CaptainOrangeSparrow/early-fire-detection-classifier/data-recording/test_recordings/recording_test1_25fps_2026-01-25_001_1769378462_16-01-02/adc.csv

frame_idx | t_sample_perf_counter | t_reg_frame | t_ir_frame | t_adc_sweep | adc_sweep_dt_s | adc0_ch0 | adc0_ch1 | adc0_ch2 | adc0_ch3 | adc1_ch0 | adc1_ch1 | adc1_ch2 | adc1_ch3
0 | 330822.027834353 | 330821.990827732 | 330821.979749989 | 330822.005690260 | 0.033709 | 1766 | 276 | 525 | 4731 | 4698 | 4576 | 4306 | 4996
1 | 330822.054127146 | 330822.030868044 | 330822.028520774 | 330822.005690260 | 0.033709 | 1766 | 276 | 525 | 4731 | 4698 | 4576 | 4306 | 4996
2 | 330822.098113978 | 330822.070159758 | 330822.059541134 | 330822.054615641 | 0.048897 | 1768 | 278 | 415 | 4648 | 4649 | 5047 | 4873 | 4268
3 | 330822.135324798 | 330822.110263209 | 330822.103432507 | 330822.091736442 | 0.037081 | 1766 | 278 | 469 | 4710 | 4795 | 4627 | 4168 | 5340
4 | 330822.172963694 | 330822.151891794 | 330822.140606781 | 330822.141824866 | 0.050006 | 1768 | 276 | 37 | 4605 | 4780 | 5144 | 4369 | 5233
5 | 330822.211742912 | 330822.191142963 | 330822.180607316 | 330822.181264712 | 0.039399 | 1767 | 279 | 423 | 4747 | 4698 | 4198 | 5421 | 4541
6 | 330822.252840793 | 330822.230302481 | 330822.220466344 | 330822.224948879 | 0.043629 | 1767 | 278 | 275 | 4694 | 4779 | 4375 | 4636 | 5089
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
