CaptainOrangeSparrow/early-fire-detection-classifier/data-recording/test_recordings/recording_test2_25fps_2026-01-26_001_1769410458_00-54-18/adc.csv

frame_idx | t_sample_perf_counter | t_reg_frame | t_ir_frame | t_adc_sweep | adc_sweep_dt_s | adc0_ch0 | adc0_ch1 | adc0_ch2 | adc0_ch3 | adc1_ch0 | adc1_ch1 | adc1_ch2 | adc1_ch3 | ir_min | ir_max | ir_avg | ir_center
0 | 362818.315297676 | 362818.274354627 | 362818.274255493 | 362818.278961247 | 0.032010 | 1736 | 286 | 373 | 4764 | 4706 | 4060 | 4685 | 5079 | 29.54 | 34.85 | 29.16 | 31.79 | INFERNO
1 | 362818.346244781 | 362818.336293317 | 362818.321560484 | 362818.325076888 | 0.046095 | 1732 | 284 | 395 | 4753 | 4766 | 4381 | 4127 | 4689 | 29.54 | 34.85 | 29.16 | 31.79 | INFERNO
2 | 362818.375747725 | 362818.336293317 | 362818.355587618 | 362818.362441390 | 0.037324 | 1734 | 285 | 326 | 4765 | 4712 | 4212 | 4680 | 5129 | 29.54 | 34.85 | 29.16 | 31.79 | INFERNO
3 | 362818.411751777 | 362818.403582482 | 362818.392606656 | 362818.405002803 | 0.042525 | 1734 | 286 | 156 | 4703 | 4614 | 5159 | 4792 | 4072 | 29.54 | 34.91 | 29.16 | 31.79 | INFERNO
4 | 362818.451165835 | 362818.435829655 | 362818.433273070 | 362818.405002803 | 0.042525 | 1734 | 286 | 156 | 4703 | 4614 | 5159 | 4792 | 4072 | 29.54 | 34.91 | 29.16 | 31.85 | INFERNO
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
