CaptainOrangeSparrow/early-fire-detection-classifier/data-recording/test_recordings/recording_test3_25fps_2026-01-26_004_1769415911_02-25-11/adc.csv

frame_idx | t_sample_perf_counter | t_reg_frame | t_ir_frame | t_adc_sweep | adc_sweep_dt_s | adc0_ch0 | adc0_ch1 | adc0_ch2 | adc0_ch3 | adc1_ch0 | adc1_ch1 | adc1_ch2 | adc1_ch3 | ir_min | ir_max | ir_avg | ir_center
0 | 368270.703455939 | 368270.672152276 | 368270.657761993 | 368270.662456597 | 0.029226 | 1750 | 286 | 345 | 4730 | 4745 | 4840 | 4552 | 4217 | 28.662500000000023 | 38.85000000000002 | 31.905227915446005 | 30.787500000000023
1 | 368270.741902709 | 368270.707983723 | 368270.695729905 | 368270.706421223 | 0.043924 | 1748 | 285 | 152 | 4675 | 4736 | 5021 | 4195 | 4840 | 28.662500000000023 | 38.85000000000002 | 31.90362701416018 | 30.787500000000023
2 | 368270.781056152 | 368270.741982071 | 368270.736752607 | 368270.746458814 | 0.039984 | 1749 | 285 | 189 | 4731 | 4667 | 5036 | 4758 | 4454 | 28.662500000000023 | 38.85000000000002 | 31.905603027343773 | 30.787500000000023
3 | 368270.808612145 | 368270.778411964 | 368270.778609728 | 368270.784546505 | 0.038049 | 1747 | 286 | 158 | 4716 | 4793 | 4839 | 4097 | 5117 | 28.662500000000023 | 38.85000000000002 | 31.90813471476241 | 30.787500000000023
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
