CaptainOrangeSparrow/early-fire-detection-classifier/data-recording/test_recordings/recording_test4_25fps_2026-01-26_006_1769417922_02-58-42/adc.csv

frame_idx | t_sample_perf_counter | t_reg_frame | t_ir_frame | t_adc_sweep | adc_sweep_dt_s | adc0_ch0 | adc0_ch1 | adc0_ch2 | adc0_ch3 | adc1_ch0 | adc1_ch1 | adc1_ch2 | adc1_ch3 | ir_min | ir_max | ir_avg | ir_center
0 | 370282.103740128 | 370282.087772986 | 370282.070901916 | 370282.071093409 | 0.032481 | 1765 | 286 | 156 | 4676 | 4597 | 4967 | 5038 | 4580 | 28.787500000000023 | 39.66250000000002 | 32.59181493123373 | 35.60000000000002
1 | 370282.134913529 | 370282.119331005 | 370282.121138348 | 370282.122146151 | 0.051032 | 1764 | 287 | 149 | 4679 | 4758 | 4979 | 5207 | 4467 | 28.787500000000023 | 39.60000000000002 | 32.59319966634115 | 35.66250000000002
2 | 370282.174606962 | 370282.153983537 | 370282.151795159 | 370282.162097576 | 0.039929 | 1763 | 287 | 151 | 4648 | 4815 | 4804 | 4159 | 4946 | 28.662500000000023 | 39.60000000000002 | 32.59789174397787 | 35.66250000000002
3 | 370282.215379016 | 370282.189044624 | 370282.193560103 | 370282.201662334 | 0.039540 | 1762 | 287 | 372 | 4745 | 4722 | 4273 | 4955 | 4913 | 28.787500000000023 | 39.60000000000002 | 32.59856948852541 | 35.66250000000002
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
