CaptainOrangeSparrow/early-fire-detection-classifier/data-recording/test_recordings/recording_test4_25fps_2026-01-26_008_1769418220_03-03-40/adc.csv

frame_idx | t_sample_perf_counter | t_reg_frame | t_ir_frame | t_adc_sweep | adc_sweep_dt_s | adc0_ch0 | adc0_ch1 | adc0_ch2 | adc0_ch3 | adc1_ch0 | adc1_ch1 | adc1_ch2 | adc1_ch3 | ir_min | ir_max | ir_avg | ir_center
0 | 370579.990639733 | 370579.981060264 | 370579.969358592 | 370579.971925576 | 0.034163 | 1762 | 286 | 342 | 4736 | 4790 | 4689 | 4121 | 4773 | 28.412500000000023 | 39.97500000000002 | 33.46427815755209 | 34.16250000000002
1 | 370580.021041448 | 370579.981060264 | 370580.003070193 | 370580.010112342 | 0.038144 | 1760 | 286 | 394 | 4757 | 4697 | 4074 | 4895 | 5138 | 28.412500000000023 | 39.91250000000002 | 33.46760203043624 | 34.10000000000002
2 | 370580.057584488 | 370580.048676398 | 370580.042907949 | 370580.047195525 | 0.037045 | 1758 | 289 | 188 | 4705 | 4571 | 4800 | 5155 | 4717 | 28.412500000000023 | 39.91250000000002 | 33.469607289632165 | 34.16250000000002
3 | 370580.098984943 | 370580.081017304 | 370580.083453660 | 370580.084930150 | 0.037696 | 1761 | 287 | 153 | 4648 | 4710 | 5078 | 4811 | 3926 | 28.412500000000023 | 39.97500000000002 | 33.46836751302084 | 34.16250000000002
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
