CaptainOrangeSparrow/early-fire-detection-classifier/data-recording/test_recordings/recording_test4_25fps_2026-01-26_009_1769418456_03-07-36/adc.csv

frame_idx | t_sample_perf_counter | t_reg_frame | t_ir_frame | t_adc_sweep | adc_sweep_dt_s | adc0_ch0 | adc0_ch1 | adc0_ch2 | adc0_ch3 | adc1_ch0 | adc1_ch1 | adc1_ch2 | adc1_ch3 | ir_min | ir_max | ir_avg | ir_center
0 | 370816.171426577 | 370816.158830439 | 370816.151630872 | 370816.151178059 | 0.031555 | 1765 | 287 | 160 | 4658 | 4723 | 5076 | 4610 | 4182 | 28.412500000000023 | 40.10000000000002 | 33.568388875325525 | 34.28750000000002
1 | 370816.208314229 | 370816.190736412 | 370816.185745325 | 370816.183391017 | 0.032158 | 1760 | 288 | 169 | 4640 | 4713 | 5067 | 4775 | 4292 | 28.412500000000023 | 40.10000000000002 | 33.57233327229818 | 34.28750000000002
2 | 370816.251142725 | 370816.222527054 | 370816.222872152 | 370816.223453417 | 0.039980 | 1763 | 288 | 155 | 4630 | 4791 | 4768 | 4183 | 4876 | 28.475000000000023 | 40.03750000000002 | 33.575635528564476 | 34.28750000000002
3 | 370816.285731015 | 370816.259526070 | 370816.264908496 | 370816.265819467 | 0.042327 | 1762 | 288 | 410 | 4767 | 4615 | 4898 | 5128 | 4460 | 28.412500000000023 | 40.03750000000002 | 33.57968165079757 | 34.28750000000002
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
