CaptainOrangeSparrow/early-fire-detection-classifier/data-recording/test_recordings/recording_test_25fps_2026-01-21_001_1769058135_23-02-15/adc.csv

frame_idx | t_sample_perf_counter | t_reg_frame | t_ir_frame | t_adc_sweep | adc_sweep_dt_s | adc0_ch0 | adc0_ch1 | adc0_ch2 | adc0_ch3 | adc1_ch0 | adc1_ch1 | adc1_ch2 | adc1_ch3
0 | 10494.949746390 | 10494.907329382 | 10494.903052842 | 10494.933231130 | 0.003040 | 1950 | 1950 | 1950 | 1951 | 4840 | 4840 | 4840 | 4788
1 | 10495.004708112 | 10494.991006075 | 10494.985168613 | 10494.991586640 | 0.007549 | -97 | -97 | 1953 | 1953 | 4575 | 4575 | 4575 | 3997
2 | 10495.057073772 | 10495.026786808 | 10495.025353987 | 10495.046790867 | 0.005011 | 1950 | 1950 | 1950 | 1951 | 4275 | 4819 | 4819 | 5286
3 | 10495.107634916 | 10495.067208830 | 10495.066076565 | 10495.094851888 | 0.003638 | 4573 | 4573 | 4573 | 1949 | 4506 | 4506 | 4506 | 4752
4 | 10495.186658412 | 10495.146546674 | 10495.143366686 | 10495.171375485 | 0.003505 | 1951 | 1951 | 1951 | 1950 | 4756 | 4756 | 4756 | 4611
5 | 10495.391040474 | 10495.348359074 | 10495.349316869 | 10495.377984029 | 0.003810 | 4557 | 4557 | 4557 | 1952 | 4020 | 4020 | 4785 | 4785
6 | 10495.638636916 | 10495.626928072 | 10495.625272300 | 10495.625371119 | 0.004291 | 4738 | 4738 | 1947 | 1947 | 4782 | 4782 | 4782 | 4505
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
