CaptainOrangeSparrow/early-fire-detection-classifier/data-recording/test_recordings/recording_test_25fps_2026-01-21_001_1769059369_23-22-49/adc.csv

frame_idx | t_sample_perf_counter | t_reg_frame | t_ir_frame | t_adc_sweep | adc_sweep_dt_s | adc0_ch0 | adc0_ch1 | adc0_ch2 | adc0_ch3 | adc1_ch0 | adc1_ch1 | adc1_ch2 | adc1_ch3
0 | 11728.372083297 | 11728.309998510 | 11728.316491082 | 11728.347690072 | 0.003868 | 1969 | 1969 | 1969 | 1969 | 4903 | 4903 | 4496 | 4496
1 | 11728.438461084 | 11728.397349920 | 11728.396888789 | 11728.415118283 | 0.004349 | 4651 | 4651 | 4651 | 1968 | 4004 | 4004 | 4004 | 4583
2 | 11728.859521468 | 11728.830881868 | 11728.833372904 | 11728.840672504 | 0.004829 | 4720 | 4720 | 1965 | 1965 | 5389 | 4825 | 4825 | 4825
3 | 11728.918410275 | 11728.872345392 | 11728.874372673 | 11728.896403218 | 0.003807 | 4697 | 4697 | 4697 | 1966 | 4485 | 4485 | 4485 | 4547
4 | 11728.975548575 | 11728.949906871 | 11728.958007962 | 11728.963948360 | 0.004277 | 4615 | 4615 | 4615 | 1970 | 4494 | 4494 | 4494 | 4486
5 | 11729.096966659 | 11729.070986387 | 11729.073584753 | 11729.086172992 | 0.004196 | 1971 | 1971 | 1971 | 1966 | 4675 | 4675 | 4797 | 4797
6 | 11729.372172756 | 11729.351712041 | 11729.353456306 | 11729.360128403 | 0.006108 | 4733 | 4733 | 1968 | 1968 | 5506 | 5506 | 5506 | 4686
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
