CaptainOrangeSparrow/early-fire-detection-classifier/data-recording/test_recordings/recording_test_25fps_2026-01-21_001_1769059793_23-29-53/adc.csv

frame_idx | t_sample_perf_counter | t_reg_frame | t_ir_frame | t_adc_sweep | adc_sweep_dt_s | adc0_ch0 | adc0_ch1 | adc0_ch2 | adc0_ch3 | adc1_ch0 | adc1_ch1 | adc1_ch2 | adc1_ch3
0 | 12152.533478815 | 12152.484226626 | 12152.516361647 | 12152.519658268 | 0.007183 | 1997 | 1997 | 1997 | 1997 | 4787 | 4787 | 4787 | 4528
1 | 12152.582394835 | 12152.565887090 | 12152.555753638 | 12152.571952544 | 0.006308 | 20688 | 20688 | 1995 | 1995 | 4458 | 4502 | 4502 | 4163
2 | 12152.678206958 | 12152.643040954 | 12152.637206642 | 12152.655680384 | 0.005038 | 3 | 3 | 3 | 4536 | 4223 | 4223 | 4548 | 4548
3 | 12152.765593732 | 12152.723165638 | 12152.717661510 | 12152.744185648 | 0.004588 | 1997 | 1997 | 1997 | 1995 | 4549 | 4912 | 4912 | 4912
4 | 12152.854543102 | 12152.805680171 | 12152.837284812 | 12152.839445246 | 0.006926 | 1995 | 1995 | 1995 | 1995 | 5150 | 5150 | 4483 | 4483
5 | 12153.002703741 | 12152.963346887 | 12152.955612051 | 12152.992445134 | 0.005571 | 4647 | 4647 | 4647 | 1993 | 4044 | 4044 | 4714 | 4714
6 | 12153.222225276 | 12153.203129855 | 12153.197926566 | 12153.208913350 | 0.005056 | 1996 | 1996 | 1996 | 1994 | 4143 | 4143 | 4854 | 4854
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
