CaptainOrangeSparrow/early-fire-detection-classifier/data-recording/test_recordings/recording_test_25fps_2026-01-21_001_1769060731_23-45-31/adc.csv

frame_idx | t_sample_perf_counter | t_reg_frame | t_ir_frame | t_adc_sweep | adc_sweep_dt_s | adc0_ch0 | adc0_ch1 | adc0_ch2 | adc0_ch3 | adc1_ch0 | adc1_ch1 | adc1_ch2 | adc1_ch3
0 | 13090.108250302 | 13090.078779330 | 13090.080440176 | 0.000000000 | 0.000000 | -1 | -1 | -1 | -1 | -1 | -1 | -1 | -1
1 | 13090.179703396 | 13090.116375029 | 13090.113490846 | 0.000000000 | 0.000000 | -1 | -1 | -1 | -1 | -1 | -1 | -1 | -1
2 | 13090.228121334 | 13090.197562077 | 13090.193768408 | 0.000000000 | 0.000000 | -1 | -1 | -1 | -1 | -1 | -1 | -1 | -1
3 | 13090.267418650 | 13090.237701866 | 13090.235034053 | 0.000000000 | 0.000000 | -1 | -1 | -1 | -1 | -1 | -1 | -1 | -1
4 | 13090.351544510 | 13090.319131366 | 13090.314027697 | 0.000000000 | 0.000000 | -1 | -1 | -1 | -1 | -1 | -1 | -1 | -1
5 | 13090.558943324 | 13090.519828295 | 13090.521465971 | 0.000000000 | 0.000000 | -1 | -1 | -1 | -1 | -1 | -1 | -1 | -1
6 | 13090.742991723 | 13090.718182367 | 13090.717482531 | 0.000000000 | 0.000000 | -1 | -1 | -1 | -1 | -1 | -1 | -1 | -1
7 | 13090.966249208 | 13090.918611593 | 13090.917398401 | 0.000000000 | 0.000000 | -1 | -1 | -1 | -1 | -1 | -1 | -1 | -1
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
