CaptainOrangeSparrow/early-fire-detection-classifier/data-recording/test_recordings/recording_test_25fps_2026-01-21_001_1769060785_23-46-25/adc.csv

frame_idx | t_sample_perf_counter | t_reg_frame | t_ir_frame | t_adc_sweep | adc_sweep_dt_s | adc0_ch0 | adc0_ch1 | adc0_ch2 | adc0_ch3 | adc1_ch0 | adc1_ch1 | adc1_ch2 | adc1_ch3
0 | 13144.571778375 | 13144.519812500 | 13144.554917660 | 0.000000000 | 0.000000 | -1 | -1 | -1 | -1 | -1 | -1 | -1 | -1
1 | 13144.632439717 | 13144.599915378 | 13144.591252905 | 0.000000000 | 0.000000 | -1 | -1 | -1 | -1 | -1 | -1 | -1 | -1
2 | 13144.960925557 | 13144.918225436 | 13144.913518809 | 0.000000000 | 0.000000 | -1 | -1 | -1 | -1 | -1 | -1 | -1 | -1
3 | 13145.023548501 | 13144.999323116 | 13144.996250575 | 0.000000000 | 0.000000 | -1 | -1 | -1 | -1 | -1 | -1 | -1 | -1
4 | 13145.075746650 | 13145.039747753 | 13145.041411922 | 0.000000000 | 0.000000 | -1 | -1 | -1 | -1 | -1 | -1 | -1 | -1
5 | 13145.159210951 | 13145.117830942 | 13145.115249737 | 0.000000000 | 0.000000 | -1 | -1 | -1 | -1 | -1 | -1 | -1 | -1
6 | 13145.278762955 | 13145.238295565 | 13145.233728405 | 0.000000000 | 0.000000 | -1 | -1 | -1 | -1 | -1 | -1 | -1 | -1
7 | 13145.465502243 | 13145.438903096 | 13145.433419926 | 0.000000000 | 0.000000 | -1 | -1 | -1 | -1 | -1 | -1 | -1 | -1
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
