CaptainOrangeSparrow/early-fire-detection-classifier/data-recording/test_recordings/recording_test_25fps_2026-01-21_001_1769060844_23-47-24/adc.csv

frame_idx | t_sample_perf_counter | t_reg_frame | t_ir_frame | t_adc_sweep | adc_sweep_dt_s | adc0_ch0 | adc0_ch1 | adc0_ch2 | adc0_ch3 | adc1_ch0 | adc1_ch1 | adc1_ch2 | adc1_ch3
0 | 13203.809093113 | 13203.793217171 | 13203.794734347 | 0.000000000 | 0.000000 | -1 | -1 | -1 | -1 | -1 | -1 | -1 | -1
1 | 13203.868863978 | 13203.829321879 | 13203.830461105 | 0.000000000 | 0.000000 | -1 | -1 | -1 | -1 | -1 | -1 | -1 | -1
2 | 13203.951978382 | 13203.910744085 | 13203.913265117 | 0.000000000 | 0.000000 | -1 | -1 | -1 | -1 | -1 | -1 | -1 | -1
3 | 13204.023067293 | 13203.990860973 | 13203.996427813 | 0.000000000 | 0.000000 | -1 | -1 | -1 | -1 | -1 | -1 | -1 | -1
4 | 13204.067859374 | 13204.030996111 | 13204.034820733 | 0.000000000 | 0.000000 | -1 | -1 | -1 | -1 | -1 | -1 | -1 | -1
5 | 13204.262495089 | 13204.231787385 | 13204.235281325 | 0.000000000 | 0.000000 | -1 | -1 | -1 | -1 | -1 | -1 | -1 | -1
6 | 13204.413368789 | 13204.390175790 | 13204.397890511 | 0.000000000 | 0.000000 | -1 | -1 | -1 | -1 | -1 | -1 | -1 | -1
7 | 13204.650052942 | 13204.630918984 | 13204.633744967 | 0.000000000 | 0.000000 | -1 | -1 | -1 | -1 | -1 | -1 | -1 | -1
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
