CaptainOrangeSparrow/early-fire-detection-classifier/data-recording/test_recordings/recording_test_25fps_2026-01-21_001_1769060875_23-47-55/adc.csv

frame_idx | t_sample_perf_counter | t_reg_frame | t_ir_frame | t_adc_sweep | adc_sweep_dt_s | adc0_ch0 | adc0_ch1 | adc0_ch2 | adc0_ch3 | adc1_ch0 | adc1_ch1 | adc1_ch2 | adc1_ch3
0 | 13234.169925595 | 13234.134877443 | 13234.151959149 | 0.000000000 | 0.000000 | -1 | -1 | -1 | -1 | -1 | -1 | -1 | -1
1 | 13234.244147372 | 13234.215262897 | 13234.192547762 | 0.000000000 | 0.000000 | -1 | -1 | -1 | -1 | -1 | -1 | -1 | -1
2 | 13234.291877915 | 13234.252970231 | 13234.271006283 | 0.000000000 | 0.000000 | -1 | -1 | -1 | -1 | -1 | -1 | -1 | -1
3 | 13234.339056766 | 13234.293351725 | 13234.311940331 | 0.000000000 | 0.000000 | -1 | -1 | -1 | -1 | -1 | -1 | -1 | -1
4 | 13234.416914313 | 13234.373577742 | 13234.391272520 | 0.000000000 | 0.000000 | -1 | -1 | -1 | -1 | -1 | -1 | -1 | -1
5 | 13234.617234714 | 13234.573635595 | 13234.591956053 | 0.000000000 | 0.000000 | -1 | -1 | -1 | -1 | -1 | -1 | -1 | -1
6 | 13234.805730744 | 13234.774198671 | 13234.752842426 | 0.000000000 | 0.000000 | -1 | -1 | -1 | -1 | -1 | -1 | -1 | -1
7 | 13235.024958528 | 13234.973918450 | 13234.998075199 | 0.000000000 | 0.000000 | -1 | -1 | -1 | -1 | -1 | -1 | -1 | -1
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
