CaptainOrangeSparrow/early-fire-detection-classifier/data-recording/test_recordings/recording_test_25fps_2026-01-21_001_1769060901_23-48-21/adc.csv

frame_idx | t_sample_perf_counter | t_reg_frame | t_ir_frame | t_adc_sweep | adc_sweep_dt_s | adc0_ch0 | adc0_ch1 | adc0_ch2 | adc0_ch3 | adc1_ch0 | adc1_ch1 | adc1_ch2 | adc1_ch3
0 | 13260.624479772 | 13260.573834315 | 13260.589705316 | 13260.597336681 | 0.033365 | 1998 | 2 | 20689 | 4708 | 4611 | 4988 | 5103 | 4613
1 | 13260.664571753 | 13260.624051291 | 13260.628662651 | 13260.643333528 | 0.045971 | 1995 | 3 | 20704 | 4562 | 4667 | 4277 | 4989 | 5025
2 | 13260.716407028 | 13260.693539687 | 13260.675488520 | 13260.697279108 | 0.053893 | 1997 | 4 | 20866 | 4763 | 4658 | 4556 | 5156 | 4633
3 | 13260.796658131 | 13260.771750538 | 13260.748824217 | 13260.780364826 | 0.035476 | 1995 | 6 | 20752 | 4722 | 4626 | 4577 | 5426 | 4606
4 | 13260.891758461 | 13260.851976903 | 13260.869713902 | 13260.864507650 | 0.031139 | 1996 | 3 | 20681 | 4688 | 4685 | 4975 | 5005 | 4643
5 | 13261.073788129 | 13261.051816729 | 13261.032791312 | 13261.034077426 | 0.038898 | 1997 | 3 | 20732 | 4743 | 4621 | 4900 | 5163 | 4497
6 | 13261.319771041 | 13261.292112744 | 13261.270557952 | 13261.272716292 | 0.036183 | 1994 | 4 | 20702 | 4695 | 4790 | 4935 | 4530 | 4369
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
