CaptainOrangeSparrow/early-fire-detection-classifier/data-recording/test_recordings/recording_test_25fps_2026-01-21_001_1769061173_23-52-53/adc.csv

frame_idx | t_sample_perf_counter | t_reg_frame | t_ir_frame | t_adc_sweep | adc_sweep_dt_s | adc0_ch0 | adc0_ch1 | adc0_ch2 | adc0_ch3 | adc1_ch0 | adc1_ch1 | adc1_ch2 | adc1_ch3
0 | 13532.328915586 | 13532.278973782 | 13532.296135239 | 13532.286956327 | 0.032111 | 1991 | 3 | 13526 | 4643 | 4729 | 5203 | 4587 | 4280
1 | 13532.390480592 | 13532.360671801 | 13532.335706660 | 13532.363342666 | 0.030755 | 1986 | 0 | 13598 | 4739 | 4698 | 4280 | 4970 | 4902
2 | 13532.424127076 | 13532.398073638 | 13532.385028038 | 13532.408712295 | 0.045306 | 1987 | 3 | 13637 | 4668 | 4771 | 4768 | 3960 | 5002
3 | 13532.462839880 | 13532.438413078 | 13532.419274435 | 13532.450180866 | 0.041420 | 1988 | -1 | 13531 | 4730 | 4607 | 4813 | 5288 | 4648
4 | 13532.635806824 | 13532.598479168 | 13532.618023919 | 13532.611270447 | 0.039900 | 1986 | 3 | 13578 | 4756 | 4768 | 4592 | 4202 | 5207
5 | 13532.855988992 | 13532.838044347 | 13532.821848811 | 13532.846434119 | 0.040108 | 1986 | 4 | 13674 | 4782 | 4751 | 4398 | 4857 | 5313
6 | 13533.037018806 | 13532.997933497 | 13533.016021863 | 13533.002207060 | 0.034210 | 1988 | 4 | 13522 | 4675 | 4658 | 4962 | 4957 | 4556
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
