CaptainOrangeSparrow/early-fire-detection-classifier/data-recording/test_recordings/recording_test_25fps_2026-01-21_002_1769061404_235644/adc.csv

frame_idx | t_sample_perf_counter | t_reg_frame | t_ir_frame | t_adc_sweep | adc_sweep_dt_s | adc0_ch0 | adc0_ch1 | adc0_ch2 | adc0_ch3 | adc1_ch0 | adc1_ch1 | adc1_ch2 | adc1_ch3
0 | 13763.098874054 | 13763.069077641 | 13763.047702767 | 13763.062578204 | 0.031684 | 1986 | 4 | 13527 | 4698 | 4752 | 4909 | 4448 | 4456
1 | 13763.161218119 | 13763.108725184 | 13763.123960995 | 13763.141241923 | 0.032686 | 1985 | 3 | 13511 | 4673 | 4652 | 4988 | 4962 | 4583
2 | 13763.225843508 | 13763.188602640 | 13763.205852558 | 13763.192454012 | 0.051168 | 1983 | 2 | 13553 | 4712 | 4629 | 4988 | 5147 | 4334
3 | 13763.306372076 | 13763.269167723 | 13763.285358696 | 13763.285071543 | 0.038180 | 1985 | 1 | 13629 | 4745 | 4799 | 4609 | 4199 | 5183
4 | 13763.382080126 | 13763.349049500 | 13763.364989130 | 13763.335657609 | 0.050468 | 1983 | 3 | 13552 | 4694 | 4814 | 4731 | 4691 | 5048
5 | 13763.569840494 | 13763.548449331 | 13763.524516893 | 13763.539019955 | 0.037428 | 1985 | 1 | 13693 | 4759 | 4674 | 4662 | 5140 | 4869
6 | 13763.756797965 | 13763.708952514 | 13763.725343564 | 13763.732754800 | 0.037680 | 1982 | 3 | 13516 | 4662 | 4744 | 4827 | 4190 | 4844
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
