CaptainOrangeSparrow/early-fire-detection-classifier/data-recording/test_recordings/recording_test_25fps_2026-01-22_001_1769061718_00-01-58/adc.csv

frame_idx | t_sample_perf_counter | t_reg_frame | t_ir_frame | t_adc_sweep | adc_sweep_dt_s | adc0_ch0 | adc0_ch1 | adc0_ch2 | adc0_ch3 | adc1_ch0 | adc1_ch1 | adc1_ch2 | adc1_ch3
0 | 14078.137531606 | 14078.090524640 | 14078.105551160 | 14078.089919166 | 0.032888 | 1984 | 4 | 13536 | 4725 | 4749 | 4953 | 4471 | 4448
1 | 14078.193834013 | 14078.168635682 | 14078.145688519 | 14078.136715368 | 0.046763 | 1984 | 1 | 13608 | 4734 | 4759 | 4742 | 4110 | 5716
2 | 14078.248774807 | 14078.209787658 | 14078.230323132 | 14078.233080313 | 0.039707 | 1983 | 1 | 13604 | 4726 | 4675 | 4472 | 5223 | 4748
3 | 14078.296955216 | 14078.249022501 | 14078.271891996 | 14078.233080313 | 0.039707 | 1983 | 1 | 13604 | 4726 | 4675 | 4472 | 5223 | 4748
4 | 14078.926494278 | 14078.888375787 | 14078.908781045 | 14078.905919090 | 0.030957 | 1982 | 3 | 13634 | 4725 | 4786 | 4823 | 4499 | 4428
5 | 14078.989621522 | 14078.968742093 | 14078.953090417 | 14078.954793490 | 0.048830 | 1982 | -2 | 13534 | 4656 | 4689 | 5359 | 4792 | 4060
6 | 14079.078909840 | 14079.049244567 | 14079.029328936 | 14079.038489714 | 0.037861 | 1981 | 5 | 13524 | 4686 | 4758 | 5062 | 4455 | 4441
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
