CaptainOrangeSparrow/early-fire-detection-classifier/data-recording/test_recordings/recording_test_25fps_2026-01-22_001_1769114525_14-42-S/adc.csv

frame_idx | t_sample_perf_counter | t_reg_frame | t_ir_frame | t_adc_sweep | adc_sweep_dt_s | adc0_ch0 | adc0_ch1 | adc0_ch2 | adc0_ch3 | adc1_ch0 | adc1_ch1 | adc1_ch2 | adc1_ch3
0 | 66885.022751207 | 66884.975316346 | 66885.000980807 | 0.000000000 | 0.000000 | -1 | -1 | -1 | -1 | -1 | -1 | -1 | -1
1 | 66885.047814307 | 66885.022344604 | 66885.036731790 | 0.000000000 | 0.000000 | -1 | -1 | -1 | -1 | -1 | -1 | -1 | -1
2 | 66885.087453847 | 66885.055245171 | 66885.079211601 | 0.000000000 | 0.000000 | -1 | -1 | -1 | -1 | -1 | -1 | -1 | -1
3 | 66885.128922206 | 66885.096389681 | 66885.119409524 | 0.000000000 | 0.000000 | -1 | -1 | -1 | -1 | -1 | -1 | -1 | -1
4 | 66885.166780192 | 66885.135564247 | 66885.156867051 | 0.000000000 | 0.000000 | -1 | -1 | -1 | -1 | -1 | -1 | -1 | -1
5 | 66885.206789246 | 66885.175900734 | 66885.156867051 | 0.000000000 | 0.000000 | -1 | -1 | -1 | -1 | -1 | -1 | -1 | -1
6 | 66885.252116976 | 66885.215935933 | 66885.201308100 | 0.000000000 | 0.000000 | -1 | -1 | -1 | -1 | -1 | -1 | -1 | -1
7 | 66885.286006467 | 66885.255807863 | 66885.242317598 | 0.000000000 | 0.000000 | -1 | -1 | -1 | -1 | -1 | -1 | -1 | -1
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
