CaptainOrangeSparrow/early-fire-detection-classifier/data-recording/test_recordings/recording_test_25fps_2026-01-22_002_1769061761_00-02-41/adc.csv

frame_idx | t_sample_perf_counter | t_reg_frame | t_ir_frame | t_adc_sweep | adc_sweep_dt_s | adc0_ch0 | adc0_ch1 | adc0_ch2 | adc0_ch3 | adc1_ch0 | adc1_ch1 | adc1_ch2 | adc1_ch3
0 | 14120.958023063 | 14120.920283903 | 14120.945399852 | 14120.920594033 | 0.031308 | 1986 | 4 | 13559 | 4731 | 4619 | 4574 | 4993 | 4939
1 | 14120.988179105 | 14120.959725335 | 14120.945399852 | 14120.963343684 | 0.042717 | 1982 | 1 | 13627 | 4729 | 4671 | 4009 | 5584 | 4547
2 | 14121.027939403 | 14120.999285589 | 14120.989681686 | 14121.002028817 | 0.038645 | 1987 | 3 | 13557 | 4705 | 4793 | 4164 | 4788 | 5246
3 | 14121.066319526 | 14121.039538075 | 14121.030021441 | 14121.040704637 | 0.038635 | 1983 | -1 | 13665 | 4768 | 4674 | 5034 | 5102 | 4640
4 | 14121.104875916 | 14121.080596782 | 14121.071579504 | 14121.080276252 | 0.039498 | 1984 | 4 | 13528 | 4704 | 4637 | 4924 | 4254 | 4583
5 | 14121.146838738 | 14121.119498663 | 14121.109476880 | 14121.121078400 | 0.040769 | 1985 | 1 | 13535 | 4682 | 4780 | 4047 | 4964 | 5023
6 | 14121.189246833 | 14121.159510303 | 14121.152993710 | 14121.161461741 | 0.040312 | 1982 | 2 | 13650 | 4744 | 4707 | 5258 | 4699 | 4016
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
