CaptainOrangeSparrow/early-fire-detection-classifier/data-recording/test_recordings/recording_test_25fps_2026-01-22_002_1769114601_14-43-S/adc.csv

frame_idx | t_sample_perf_counter | t_reg_frame | t_ir_frame | t_adc_sweep | adc_sweep_dt_s | adc0_ch0 | adc0_ch1 | adc0_ch2 | adc0_ch3 | adc1_ch0 | adc1_ch1 | adc1_ch2 | adc1_ch3
0 | 66960.547984917 | 66960.501830368 | 66960.510715131 | 66960.515675270 | 0.033969 | 1931 | 2 | 269 | 4747 | 4769 | 4234 | 4589 | 4993
1 | 66960.571808148 | 66960.548209819 | 66960.553535025 | 66960.561599540 | 0.045901 | 1931 | 4 | 271 | 4714 | 4783 | 5491 | 4281 | 4659
2 | 66960.612999964 | 66960.581550150 | 66960.589472677 | 66960.601274674 | 0.039630 | 1934 | 3 | 273 | 4773 | 4645 | 4560 | 4911 | 5160
3 | 66960.655411687 | 66960.621358984 | 66960.629173316 | 66960.637324425 | 0.036005 | 1931 | -1 | 273 | 4717 | 4631 | 4563 | 5258 | 4715
4 | 66960.695016803 | 66960.661327758 | 66960.670027331 | 66960.680720848 | 0.043358 | 1933 | 3 | 271 | 4661 | 4772 | 4974 | 4211 | 4930
5 | 66960.733622338 | 66960.701088398 | 66960.710781983 | 66960.717771812 | 0.037019 | 1932 | 2 | 273 | 4758 | 4707 | 4287 | 4709 | 5207
6 | 66960.780778547 | 66960.741062388 | 66960.751760577 | 66960.757153977 | 0.039332 | 1931 | 3 | 270 | 4694 | 4583 | 5172 | 4930 | 4483
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
