CaptainOrangeSparrow/early-fire-detection-classifier/data-recording/test_recordings/recording_test_25fps_2026-01-22_003_1769062595_00-16-S/adc.csv

frame_idx | t_sample_perf_counter | t_reg_frame | t_ir_frame | t_adc_sweep | adc_sweep_dt_s | adc0_ch0 | adc0_ch1 | adc0_ch2 | adc0_ch3 | adc1_ch0 | adc1_ch1 | adc1_ch2 | adc1_ch3
0 | 14954.169377008 | 14954.133656756 | 14954.152132155 | 14954.134258925 | 0.033979 | 1982 | 3 | 13531 | 4646 | 4663 | 5106 | 4810 | 4141
1 | 14954.196486065 | 14954.174677489 | 14954.152132155 | 14954.182824146 | 0.048539 | 1984 | 3 | 13582 | 4734 | 4485 | 5069 | 4987 | 4507
2 | 14954.233281344 | 14954.213395530 | 14954.192592287 | 14954.223443028 | 0.040559 | 1979 | 5 | 13593 | 4713 | 4771 | 4876 | 4021 | 4931
3 | 14954.273628453 | 14954.252876633 | 14954.228565815 | 14954.259234638 | 0.035761 | 1980 | 3 | 13661 | 4763 | 4678 | 4094 | 4772 | 5168
4 | 14954.314986494 | 14954.294041333 | 14954.273818019 | 14954.298141508 | 0.038876 | 1980 | 5 | 13513 | 4697 | 4634 | 4918 | 5083 | 4622
5 | 14954.353627703 | 14954.332570287 | 14954.315055869 | 14954.335986759 | 0.037811 | 1982 | 2 | 13516 | 4678 | 4787 | 5098 | 4605 | 4160
6 | 14954.395513451 | 14954.372443066 | 14954.353947796 | 14954.371812705 | 0.035776 | 1982 | 6 | 13546 | 4700 | 4779 | 4669 | 4176 | 4635
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
