CaptainOrangeSparrow/early-fire-detection-classifier/data-recording/test_recordings/recording_test_25fps_2026-01-22_003_1769114613_14-43-S/adc.csv

frame_idx | t_sample_perf_counter | t_reg_frame | t_ir_frame | t_adc_sweep | adc_sweep_dt_s | adc0_ch0 | adc0_ch1 | adc0_ch2 | adc0_ch3 | adc1_ch0 | adc1_ch1 | adc1_ch2 | adc1_ch3
0 | 66973.365201706 | 66973.321481080 | 66973.312226963 | 66973.317490632 | 0.033312 | 1931 | 1 | 272 | 4747 | 4717 | 4029 | 4851 | 5123
1 | 66973.388830788 | 66973.365511410 | 66973.365586004 | 66973.365319949 | 0.047809 | 1934 | 3 | 269 | 4758 | 4743 | 4115 | 4717 | 5204
2 | 66973.425139172 | 66973.401547563 | 66973.391766103 | 66973.403765641 | 0.038371 | 1934 | 0 | 271 | 4759 | 4749 | 4604 | 5110 | 4733
3 | 66973.466062599 | 66973.441321389 | 66973.430511996 | 66973.438336120 | 0.034540 | 1933 | 2 | 273 | 4704 | 4680 | 4895 | 5173 | 4559
4 | 66973.504691816 | 66973.480765605 | 66973.472909192 | 66973.476609360 | 0.038206 | 1932 | 3 | 271 | 4662 | 4643 | 5704 | 4348 | 4526
5 | 66973.543585329 | 66973.520702892 | 66973.514035120 | 66973.516596920 | 0.039930 | 1934 | 2 | 267 | 4732 | 4812 | 4078 | 4847 | 5205
6 | 66973.588663561 | 66973.560714612 | 66973.549485976 | 66973.554976595 | 0.038336 | 1927 | 2 | 273 | 4761 | 4678 | 4359 | 5309 | 4524
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
