CaptainOrangeSparrow/early-fire-detection-classifier/data-recording/test_recordings/recording_test_25fps_2026-01-22_004_1769062650_00-17-S/adc.csv

frame_idx | t_sample_perf_counter | t_reg_frame | t_ir_frame | t_adc_sweep | adc_sweep_dt_s | adc0_ch0 | adc0_ch1 | adc0_ch2 | adc0_ch3 | adc1_ch0 | adc1_ch1 | adc1_ch2 | adc1_ch3
0 | 15009.134771512 | 15009.100676203 | 15009.107659802 | 15009.119118088 | 0.037334 | 1991 | 2 | 13671 | 4758 | 4719 | 5062 | 4953 | 4554
1 | 15009.167170449 | 15009.141177866 | 15009.142440897 | 15009.119118088 | 0.037334 | 1991 | 2 | 13671 | 4758 | 4719 | 5062 | 4953 | 4554
2 | 15009.200804129 | 15009.181735689 | 15009.185098321 | 15009.162092853 | 0.042937 | 1990 | 4 | 13663 | 4753 | 4733 | 4382 | 4525 | 5030
3 | 15009.241955643 | 15009.221532877 | 15009.224173914 | 15009.209304292 | 0.047173 | 1989 | 7 | 13641 | 4607 | 4740 | 5250 | 4214 | 4847
4 | 15009.281729119 | 15009.261203889 | 15009.263470401 | 15009.251988403 | 0.042578 | 1989 | 0 | 13660 | 4772 | 4715 | 4553 | 5058 | 4568
5 | 15009.318610679 | 15009.301367762 | 15009.302617034 | 15009.289305929 | 0.037158 | 1989 | 5 | 13534 | 4660 | 4675 | 5262 | 4543 | 4353
6 | 15009.364441392 | 15009.341530004 | 15009.343636389 | 15009.325822852 | 0.036404 | 1986 | -1 | 13593 | 4734 | 4766 | 4851 | 4041 | 4823
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
