CaptainOrangeSparrow/early-fire-detection-classifier/data-recording/test_recordings/recording_test_25fps_2026-01-22_004_1769114778_14-46-S/adc.csv

frame_idx | t_sample_perf_counter | t_reg_frame | t_ir_frame | t_adc_sweep | adc_sweep_dt_s | adc0_ch0 | adc0_ch1 | adc0_ch2 | adc0_ch3 | adc1_ch0 | adc1_ch1 | adc1_ch2 | adc1_ch3
0 | 67137.909444464 | 67137.864468362 | 67137.858328763 | 67137.888104750 | 0.031274 | 1933 | 3 | 271 | 4742 | 4786 | 4646 | 4194 | 4796
1 | 67137.944719745 | 67137.907478392 | 67137.934291927 | 67137.931807088 | 0.043681 | 1932 | 0 | 272 | 4642 | 4694 | 4972 | 4954 | 4518
2 | 67137.977061470 | 67137.945320754 | 67137.934291927 | 67137.931807088 | 0.043681 | 1932 | 0 | 272 | 4642 | 4694 | 4972 | 4954 | 4518
3 | 67138.009919657 | 67137.984555252 | 67137.978245344 | 67137.977656623 | 0.045808 | 1933 | 1 | 271 | 4741 | 4812 | 4673 | 4159 | 5194
4 | 67138.049573687 | 67138.024641614 | 67138.015709071 | 67138.018845513 | 0.041154 | 1930 | 3 | 271 | 4751 | 4684 | 4483 | 5473 | 4358
5 | 67138.086955908 | 67138.064617350 | 67138.056710563 | 67138.060379212 | 0.041494 | 1932 | 3 | 270 | 4682 | 4762 | 5144 | 4321 | 4942
6 | 67138.130210617 | 67138.105783775 | 67138.095612604 | 67138.098713941 | 0.038263 | 1932 | 2 | 272 | 4721 | 4685 | 4254 | 5243 | 4348
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
