CaptainOrangeSparrow/early-fire-detection-classifier/data-recording/test_recordings/recording_test_25fps_2026-01-22_005_1769062789_00-19-S/adc.csv

frame_idx | t_sample_perf_counter | t_reg_frame | t_ir_frame | t_adc_sweep | adc_sweep_dt_s | adc0_ch0 | adc0_ch1 | adc0_ch2 | adc0_ch3 | adc1_ch0 | adc1_ch1 | adc1_ch2 | adc1_ch3
0 | 15148.409055363 | 15148.367037143 | 15148.370917665 | 15148.384789253 | 0.033062 | 1987 | 0 | 13651 | 4755 | 4667 | 4313 | 4965 | 5072
1 | 15148.437246795 | 15148.408021536 | 15148.415476116 | 15148.426989137 | 0.042156 | 1982 | 4 | 13688 | 4692 | 4782 | 5042 | 4663 | 4199
2 | 15148.471979108 | 15148.445437728 | 15148.444790527 | 15148.464156400 | 0.037128 | 1982 | 4 | 13693 | 4761 | 4794 | 4677 | 4091 | 4841
3 | 15148.517001400 | 15148.486661354 | 15148.486934539 | 15148.497766118 | 0.033578 | 1981 | 2 | 13678 | 4770 | 4757 | 4586 | 4245 | 4925
4 | 15148.553867254 | 15148.526256431 | 15148.527338642 | 15148.543961085 | 0.046160 | 1983 | 3 | 13694 | 4707 | 4700 | 5029 | 4815 | 3998
5 | 15148.594512510 | 15148.567205304 | 15148.568523835 | 15148.584898213 | 0.040862 | 1984 | 5 | 13678 | 4770 | 4692 | 4225 | 5059 | 5095
6 | 15148.636432329 | 15148.605720667 | 15148.604900665 | 15148.584898213 | 0.040862 | 1984 | 5 | 13678 | 4770 | 4692 | 4225 | 5059 | 5095
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
