CaptainOrangeSparrow/early-fire-detection-classifier/data-recording/test_recordings/recording_test_25fps_2026-01-22_005_1769114870_14-47-S/adc.csv

frame_idx | t_sample_perf_counter | t_reg_frame | t_ir_frame | t_adc_sweep | adc_sweep_dt_s | adc0_ch0 | adc0_ch1 | adc0_ch2 | adc0_ch3 | adc1_ch0 | adc1_ch1 | adc1_ch2 | adc1_ch3
0 | 67229.323568406 | 67229.279905262 | 67229.290394908 | 67229.309239674 | 0.036208 | 1939 | 3 | 273 | 4614 | 4704 | 5107 | 4868 | 4433
1 | 67229.357132956 | 67229.323120073 | 67229.329532066 | 67229.309239674 | 0.036208 | 1939 | 3 | 273 | 4614 | 4704 | 5107 | 4868 | 4433
2 | 67229.388368030 | 67229.360958794 | 67229.368558500 | 67229.357712620 | 0.048416 | 1937 | 1 | 273 | 4762 | 4690 | 4299 | 4925 | 5105
3 | 67229.430961543 | 67229.400444345 | 67229.408226073 | 67229.396193919 | 0.038436 | 1935 | 4 | 270 | 4685 | 4637 | 4916 | 4536 | 4456
4 | 67229.470129710 | 67229.440268979 | 67229.446897522 | 67229.441478262 | 0.045168 | 1934 | 2 | 270 | 4738 | 4787 | 4277 | 5369 | 4563
5 | 67229.509552732 | 67229.480134254 | 67229.486435075 | 67229.482706360 | 0.041178 | 1935 | 3 | 271 | 4667 | 4748 | 4544 | 4312 | 4936
6 | 67229.553866166 | 67229.520060298 | 67229.527674885 | 67229.518160019 | 0.035427 | 1937 | 2 | 271 | 4726 | 4800 | 4731 | 4621 | 5188
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
