CaptainOrangeSparrow/early-fire-detection-classifier/data-recording/test_recordings/recording_test_25fps_2026-01-22_006_1769062917_00-21-S/adc.csv

frame_idx | t_sample_perf_counter | t_reg_frame | t_ir_frame | t_adc_sweep | adc_sweep_dt_s | adc0_ch0 | adc0_ch1 | adc0_ch2 | adc0_ch3 | adc1_ch0 | adc1_ch1 | adc1_ch2 | adc1_ch3
0 | 15277.052470458 | 15277.016034530 | 15277.035793692 | 15277.034761523 | 0.032195 | 1984 | 3 | 13626 | 4766 | 4699 | 4064 | 4943 | 5188
1 | 15277.082499894 | 15277.056400383 | 15277.035793692 | 15277.034761523 | 0.032195 | 1984 | 3 | 13626 | 4766 | 4699 | 4064 | 4943 | 5188
2 | 15277.116255223 | 15277.095956726 | 15277.110564193 | 15277.087398725 | 0.052560 | 1984 | 0 | 13637 | 4736 | 4786 | 4731 | 4201 | 4876
3 | 15277.158572872 | 15277.135952593 | 15277.151077345 | 15277.125763953 | 0.038276 | 1984 | 3 | 13563 | 4705 | 4617 | 4831 | 4693 | 4120
4 | 15277.195833577 | 15277.175989325 | 15277.151077345 | 15277.165257767 | 0.039437 | 1981 | 2 | 13528 | 4670 | 4729 | 5134 | 4072 | 4961
5 | 15277.238079322 | 15277.216138154 | 15277.196525712 | 15277.202974221 | 0.037616 | 1981 | 0 | 13700 | 4741 | 4728 | 4343 | 5040 | 5132
6 | 15277.283226566 | 15277.256154310 | 15277.238819521 | 15277.243290124 | 0.040259 | 1982 | 2 | 13570 | 4704 | 4577 | 4762 | 5400 | 4165
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
