CaptainOrangeSparrow/early-fire-detection-classifier/data-recording/test_recordings/recording_test_25fps_2026-01-22_007_1769062937_00-22-S/adc.csv

frame_idx | t_sample_perf_counter | t_reg_frame | t_ir_frame | t_adc_sweep | adc_sweep_dt_s | adc0_ch0 | adc0_ch1 | adc0_ch2 | adc0_ch3 | adc1_ch0 | adc1_ch1 | adc1_ch2 | adc1_ch3
0 | 15296.952172247 | 15296.915582300 | 15296.913133570 | 15296.922682597 | 0.031423 | 1987 | 0 | 13535 | 4697 | 4748 | 4970 | 4530 | 4311
1 | 15296.977351228 | 15296.955985183 | 15296.957535311 | 15296.966562028 | 0.043845 | 1985 | 4 | 13518 | 4679 | 4629 | 4782 | 5153 | 4733
2 | 15297.016152238 | 15296.995752827 | 15296.991119243 | 15297.003007078 | 0.036391 | 1985 | 1 | 13507 | 4709 | 4612 | 5105 | 4852 | 4442
3 | 15297.061067104 | 15297.035480951 | 15297.028256076 | 15297.038677848 | 0.035632 | 1984 | 0 | 13537 | 4650 | 4748 | 5172 | 4591 | 4197
4 | 15297.099575889 | 15297.075496502 | 15297.070223295 | 15297.079716962 | 0.041017 | 1984 | 4 | 13526 | 4665 | 4746 | 4345 | 4656 | 5070
5 | 15297.136221039 | 15297.115444470 | 15297.109175701 | 15297.121306131 | 0.041529 | 1985 | 0 | 13663 | 4724 | 4600 | 5124 | 4779 | 4068
6 | 15297.182066572 | 15297.155720538 | 15297.149859581 | 15297.160604780 | 0.039235 | 1983 | 3 | 13520 | 4729 | 4768 | 4818 | 4077 | 5046
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
