CaptainOrangeSparrow/early-fire-detection-classifier/data-recording/test_recordings/recording_test_25fps_2026-01-22_008_1769062949_00-22-S/adc.csv

frame_idx | t_sample_perf_counter | t_reg_frame | t_ir_frame | t_adc_sweep | adc_sweep_dt_s | adc0_ch0 | adc0_ch1 | adc0_ch2 | adc0_ch3 | adc1_ch0 | adc1_ch1 | adc1_ch2 | adc1_ch3
0 | 15309.043378476 | 15309.026004239 | 15308.989742500 | 15309.008282734 | 0.034306 | 1982 | 4 | 13704 | 4760 | 4733 | 4567 | 4213 | 4997
1 | 15309.107436745 | 15309.065986051 | 15309.075247721 | 15309.088286647 | 0.033934 | 1983 | -1 | 13532 | 4689 | 4772 | 4858 | 4491 | 4428
2 | 15309.159957192 | 15309.144074266 | 15309.148764718 | 15309.137222287 | 0.048823 | 1984 | 0 | 13515 | 4663 | 4768 | 5209 | 4559 | 4280
3 | 15309.202491290 | 15309.187719512 | 15309.188839749 | 15309.181117360 | 0.043832 | 1984 | 2 | 13707 | 4744 | 4661 | 4540 | 4966 | 4778
4 | 15309.343081598 | 15309.304211220 | 15309.310402808 | 15309.300935792 | 0.038804 | 1983 | 3 | 13583 | 4742 | 4613 | 5190 | 4969 | 4374
5 | 15309.582441851 | 15309.544571932 | 15309.549973751 | 15309.531850769 | 0.037415 | 1983 | 3 | 13665 | 4770 | 4689 | 4227 | 5427 | 4690
6 | 15309.781565855 | 15309.744658571 | 15309.749043419 | 15309.742181520 | 0.033572 | 1983 | 4 | 13688 | 4774 | 4758 | 4475 | 4553 | 4983
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
