CaptainOrangeSparrow/early-fire-detection-classifier/data-recording/test_recordings/recording_test_25fps_2026-01-22_010_1769063873_00-37-S/adc.csv

frame_idx | t_sample_perf_counter | t_reg_frame | t_ir_frame | t_adc_sweep | adc_sweep_dt_s | adc0_ch0 | adc0_ch1 | adc0_ch2 | adc0_ch3 | adc1_ch0 | adc1_ch1 | adc1_ch2 | adc1_ch3
0 | 16233.121186215 | 16233.086455673 | 16233.105310541 | 16233.106944350 | 0.034630 | 2015 | 2 | 13625 | 4724 | 4662 | 4369 | 5194 | 4712
1 | 16233.151049924 | 16233.126574889 | 16233.143274588 | 16233.106944350 | 0.034630 | 2015 | 2 | 13625 | 4724 | 4662 | 4369 | 5194 | 4712
2 | 16233.189545764 | 16233.166729241 | 16233.182455472 | 16233.153239270 | 0.046261 | 2012 | 6 | 13673 | 4751 | 4765 | 4654 | 4039 | 5477
3 | 16233.233142715 | 16233.206598434 | 16233.182455472 | 16233.193414199 | 0.040135 | 2013 | 0 | 13654 | 4770 | 4679 | 4080 | 5167 | 4330
4 | 16233.270624348 | 16233.246839637 | 16233.223307157 | 16233.235837900 | 0.042350 | 2011 | 3 | 13508 | 4654 | 4673 | 5115 | 4751 | 5004
5 | 16233.309429252 | 16233.286824833 | 16233.264904081 | 16233.276353735 | 0.040470 | 2011 | 3 | 13645 | 4750 | 4726 | 4118 | 5488 | 4351
6 | 16233.355396195 | 16233.326891471 | 16233.304944862 | 16233.315539867 | 0.039076 | 2010 | 6 | 13515 | 4682 | 4691 | 5141 | 3917 | 4892
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
