CaptainOrangeSparrow/early-fire-detection-classifier/data-recording/test_recordings/recording_test_25fps_2026-01-22_011_1769064130_00-42-S/adc.csv

frame_idx | t_sample_perf_counter | t_reg_frame | t_ir_frame | t_adc_sweep | adc_sweep_dt_s | adc0_ch0 | adc0_ch1 | adc0_ch2 | adc0_ch3 | adc1_ch0 | adc1_ch1 | adc1_ch2 | adc1_ch3
0 | 16490.605205959 | 16490.570195081 | 16490.562829223 | 16490.590025491 | 0.031522 | 2008 | 1 | 13691 | 4762 | 4741 | 4536 | 4387 | 4949
1 | 16490.670667600 | 16490.650269167 | 16490.643740207 | 16490.629904752 | 0.039842 | 2011 | 7 | 13540 | 4695 | 4615 | 4868 | 5126 | 4733
2 | 16490.768629493 | 16490.730392248 | 16490.724812061 | 16490.745710898 | 0.034267 | 2007 | 2 | 13505 | 4718 | 4637 | 4851 | 5120 | 4752
3 | 16492.020821929 | 16491.970331852 | 16491.963375067 | 16491.971807590 | 0.031679 | 2007 | 3 | 13686 | 4757 | 4800 | 4534 | 4251 | 4973
4 | 16492.086410231 | 16492.051523518 | 16492.043055346 | 16492.060516767 | 0.033206 | 2007 | 2 | 13587 | 4723 | 4677 | 4434 | 4962 | 5127
5 | 16492.192639647 | 16492.170501530 | 16492.163191931 | 16492.181797845 | 0.036298 | 2009 | 0 | 13589 | 4752 | 4605 | 4898 | 5017 | 4667
6 | 16492.291517382 | 16492.250464731 | 16492.247650189 | 16492.261742294 | 0.033553 | 2007 | 2 | 13611 | 4723 | 4596 | 4739 | 5103 | 4841
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
