CaptainOrangeSparrow/early-fire-detection-classifier/data-recording/test_recordings/recording_test_25fps_2026-01-22_012_1769064270_00-44-S/adc.csv

frame_idx | t_sample_perf_counter | t_reg_frame | t_ir_frame | t_adc_sweep | adc_sweep_dt_s | adc0_ch0 | adc0_ch1 | adc0_ch2 | adc0_ch3 | adc1_ch0 | adc1_ch1 | adc1_ch2 | adc1_ch3
0 | 16631.252666431 | 16631.220190250 | 16631.229830713 | 16631.213219649 | 0.031058 | 2005 | 3 | 13687 | 4754 | 4775 | 4588 | 4254 | 4784
1 | 16631.318207902 | 16631.303418923 | 16631.274149905 | 16631.292194976 | 0.036619 | 2004 | 3 | 13514 | 4716 | 4664 | 5181 | 4658 | 4205
2 | 16631.408287940 | 16631.380238552 | 16631.389195341 | 16631.377360458 | 0.036330 | 2006 | 4 | 13529 | 4657 | 4753 | 5046 | 4520 | 4360
3 | 16631.478365744 | 16631.420375952 | 16631.437641665 | 16631.418205085 | 0.040799 | 2004 | 2 | 13522 | 4676 | 4744 | 5172 | 4686 | 5053
4 | 16633.168478849 | 16633.140477336 | 16633.150037219 | 16633.129959367 | 0.029686 | 2001 | 5 | 13686 | 4733 | 4748 | 4609 | 4208 | 4765
5 | 16633.259415014 | 16633.220350039 | 16633.229682138 | 16633.240419763 | 0.032117 | 2001 | 3 | 13523 | 4687 | 4667 | 4925 | 4953 | 4512
6 | 16633.334684631 | 16633.300308890 | 16633.310068462 | 16633.319649818 | 0.035665 | 2001 | 1 | 13688 | 4766 | 4712 | 4190 | 4985 | 5088
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
