CaptainOrangeSparrow/early-fire-detection-classifier/data-recording/test_recordings/recording_test_25fps_2026-01-22_013_1769064475_00-47-S/adc.csv

frame_idx | t_sample_perf_counter | t_reg_frame | t_ir_frame | t_adc_sweep | adc_sweep_dt_s | adc0_ch0 | adc0_ch1 | adc0_ch2 | adc0_ch3 | adc1_ch0 | adc1_ch1 | adc1_ch2 | adc1_ch3
0 | 16835.444807995 | 16835.403341411 | 16835.417683764 | 16835.416479495 | 0.031024 | 1996 | 4 | 13655 | 4766 | 4731 | 4354 | 4509 | 5053
1 | 16835.493945806 | 16835.444331498 | 16835.456783125 | 16835.455916661 | 0.039393 | 1996 | 3 | 13692 | 4775 | 4772 | 4672 | 5153 | 4794
2 | 16835.555980124 | 16835.523628820 | 16835.540103315 | 16835.535145340 | 0.034473 | 1996 | 8 | 13684 | 4747 | 4697 | 4271 | 4813 | 5360
3 | 16835.605495773 | 16835.563562547 | 16835.579362714 | 16835.585650913 | 0.050448 | 1993 | 3 | 13628 | 4736 | 4785 | 4032 | 4928 | 5324
4 | 16836.388035073 | 16836.363987179 | 16836.336532503 | 16836.354029116 | 0.030546 | 1993 | 3 | 13510 | 4709 | 4637 | 4807 | 5194 | 4803
5 | 16836.474716570 | 16836.443875210 | 16836.457530849 | 16836.438778958 | 0.037422 | 1993 | 4 | 13587 | 4737 | 4603 | 4754 | 5211 | 4663
6 | 16836.568651744 | 16836.524287325 | 16836.537373311 | 16836.551371331 | 0.033214 | 1991 | 1 | 13644 | 4753 | 4652 | 4441 | 4967 | 5048
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
