CaptainOrangeSparrow/early-fire-detection-classifier/data-recording/test_recordings/recording_test_25fps_2026-01-22_014_1769064502_00-48-S/adc.csv

frame_idx | t_sample_perf_counter | t_reg_frame | t_ir_frame | t_adc_sweep | adc_sweep_dt_s | adc0_ch0 | adc0_ch1 | adc0_ch2 | adc0_ch3 | adc1_ch0 | adc1_ch1 | adc1_ch2 | adc1_ch3
0 | 16861.834751159 | 16861.806600462 | 16861.774876960 | 16861.807148418 | 0.030238 | 2001 | 1 | 13699 | 4754 | 4759 | 4656 | 4118 | 4869
1 | 16861.876984455 | 16861.845594150 | 16861.854087646 | 16861.856253293 | 0.049087 | 2000 | 4 | 13521 | 4717 | 4747 | 4902 | 4269 | 4539
2 | 16862.201125031 | 16862.165040218 | 16862.176597570 | 16862.161348626 | 0.029657 | 1994 | 1 | 13618 | 4751 | 4671 | 4368 | 4955 | 5072
3 | 16862.255930467 | 16862.206526253 | 16862.217080977 | 16862.221083268 | 0.059680 | 1998 | 5 | 13618 | 4600 | 4557 | 4852 | 4903 | 4051
4 | 16862.299638601 | 16862.285925329 | 16862.265412480 | 16862.275864320 | 0.054740 | 1999 | 1 | 13630 | 4724 | 4815 | 5258 | 4455 | 4780
5 | 16862.360383327 | 16862.326108565 | 16862.332467326 | 16862.331662849 | 0.055710 | 1997 | 2 | 13687 | 4754 | 4727 | 3987 | 4892 | 4960
6 | 16862.548934763 | 16862.526476435 | 16862.534478393 | 16862.533056004 | 0.034512 | 1999 | 2 | 13548 | 4743 | 4652 | 4571 | 4954 | 4800
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
