CaptainOrangeSparrow/early-fire-detection-classifier/data-recording/test_recordings/recording_test_25fps_2026-01-22_015_1769064515_00-48-S/adc.csv

frame_idx | t_sample_perf_counter | t_reg_frame | t_ir_frame | t_adc_sweep | adc_sweep_dt_s | adc0_ch0 | adc0_ch1 | adc0_ch2 | adc0_ch3 | adc1_ch0 | adc1_ch1 | adc1_ch2 | adc1_ch3
0 | 16874.317738216 | 16874.294608312 | 16874.291160857 | 16874.290154164 | 0.032853 | 1997 | -1 | 13686 | 4737 | 4735 | 4424 | 4425 | 4981
1 | 16874.356418066 | 16874.334793017 | 16874.330861065 | 16874.330410232 | 0.040235 | 1996 | 7 | 13689 | 4761 | 4720 | 5024 | 5139 | 4627
2 | 16874.879268150 | 16874.853987127 | 16874.851638721 | 16874.847903960 | 0.030234 | 1998 | 2 | 13528 | 4692 | 4661 | 5026 | 4975 | 4520
3 | 16874.931571412 | 16874.893919759 | 16874.891650972 | 16874.887580039 | 0.039622 | 1994 | 1 | 13522 | 4701 | 4639 | 4931 | 4283 | 4573
4 | 16874.994764577 | 16874.973894308 | 16874.971013882 | 16874.975192499 | 0.052157 | 1995 | 3 | 13587 | 4760 | 4781 | 4330 | 4639 | 5116
5 | 16875.034993188 | 16875.014858946 | 16875.016338808 | 16875.023317208 | 0.048091 | 1994 | 0 | 13642 | 4707 | 4643 | 5240 | 4336 | 4702
6 | 16875.068458927 | 16875.054571026 | 16875.054969825 | 16875.023317208 | 0.048091 | 1994 | 0 | 13642 | 4707 | 4643 | 5240 | 4336 | 4702
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
