CaptainOrangeSparrow/early-fire-detection-classifier/data-recording/test_recordings/recording_test_25fps_2026-01-22_016_1769064569_00-49-S/adc.csv

frame_idx | t_sample_perf_counter | t_reg_frame | t_ir_frame | t_adc_sweep | adc_sweep_dt_s | adc0_ch0 | adc0_ch1 | adc0_ch2 | adc0_ch3 | adc1_ch0 | adc1_ch1 | adc1_ch2 | adc1_ch3
0 | 16928.337893754 | 16928.301600496 | 16928.287174978 | 16928.306750220 | 0.036282 | 1993 | 2 | 13515 | 4654 | 4736 | 5185 | 4636 | 4445
1 | 16928.391910667 | 16928.341527551 | 16928.366610545 | 16928.348371992 | 0.041579 | 1992 | -1 | 13518 | 4687 | 4778 | 4178 | 4967 | 4920
2 | 16928.453019581 | 16928.420826952 | 16928.411593976 | 16928.437343746 | 0.042518 | 1992 | 1 | 13529 | 4645 | 4783 | 5104 | 4717 | 4147
3 | 16928.507759464 | 16928.460982623 | 16928.489706518 | 16928.486997107 | 0.049618 | 1994 | 6 | 13510 | 4710 | 4673 | 5028 | 4842 | 4249
4 | 16928.540869662 | 16928.507842603 | 16928.527267151 | 16928.486997107 | 0.049618 | 1994 | 6 | 13510 | 4710 | 4673 | 5028 | 4842 | 4249
5 | 16928.765616475 | 16928.740630509 | 16928.726872920 | 16928.731330298 | 0.036314 | 1992 | 4 | 13652 | 4753 | 4723 | 4288 | 5132 | 4942
6 | 16928.982922249 | 16928.940884749 | 16928.929002108 | 16928.942513225 | 0.040724 | 1991 | 5 | 13530 | 4666 | 4774 | 5083 | 4193 | 4826
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
