CaptainOrangeSparrow/early-fire-detection-classifier/data-recording/test_recordings/recording_test_25fps_2026-01-22_017_1769064575_00-49-S/adc.csv

frame_idx | t_sample_perf_counter | t_reg_frame | t_ir_frame | t_adc_sweep | adc_sweep_dt_s | adc0_ch0 | adc0_ch1 | adc0_ch2 | adc0_ch3 | adc1_ch0 | adc1_ch1 | adc1_ch2 | adc1_ch3
0 | 16934.316672655 | 16934.270964943 | 16934.290128489 | 16934.284219313 | 0.030757 | 1992 | 2 | 13562 | 4724 | 4673 | 4649 | 5077 | 4929
1 | 16934.374503529 | 16934.351214297 | 16934.328296662 | 16934.326764159 | 0.042520 | 1991 | 4 | 13552 | 4720 | 4634 | 5277 | 4460 | 4407
2 | 16934.471667899 | 16934.431350623 | 16934.447460809 | 16934.426508623 | 0.036060 | 1990 | 4 | 13585 | 4753 | 4813 | 4707 | 4185 | 4715
3 | 16934.562283934 | 16934.512841078 | 16934.527716532 | 16934.514776733 | 0.039835 | 1989 | -1 | 13645 | 4773 | 4692 | 4435 | 4944 | 5180
4 | 16934.639784772 | 16934.591321792 | 16934.608224647 | 16934.598940213 | 0.035002 | 1992 | 6 | 13628 | 4765 | 4699 | 4185 | 5061 | 5096
5 | 16934.786707370 | 16934.751223390 | 16934.769598875 | 16934.763198226 | 0.040160 | 1988 | 3 | 13683 | 4766 | 4773 | 4589 | 4097 | 5088
6 | 16935.042265572 | 16934.991706643 | 16935.007695385 | 16935.000334925 | 0.036631 | 1990 | 2 | 13624 | 4763 | 4676 | 4320 | 4999 | 4944
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
