CaptainOrangeSparrow/early-fire-detection-classifier/data-recording/test_recordings/recording_test_25fps_2026-01-25_001_1769372867_14-27-S/adc.csv

frame_idx | t_sample_perf_counter | t_reg_frame | t_ir_frame | t_adc_sweep | adc_sweep_dt_s | adc0_ch0 | adc0_ch1 | adc0_ch2 | adc0_ch3 | adc1_ch0 | adc1_ch1 | adc1_ch2 | adc1_ch3
0 | 325226.572072633 | 325226.526043651 | 325226.520990203 | 325226.538477407 | 0.032879 | 1719 | 4 | 38 | 4654 | 4583 | 4876 | 5316 | 4721
1 | 325226.599307584 | 325226.572810513 | 325226.565062545 | 325226.584078727 | 0.045554 | 1717 | -2 | 40 | 4663 | 4530 | 4881 | 4780 | 5200
2 | 325226.636471376 | 325226.604715763 | 325226.603961786 | 325226.622536962 | 0.038408 | 1718 | 0 | 39 | 4657 | 4579 | 4870 | 5278 | 4610
3 | 325226.688439723 | 325226.645287060 | 325226.641537592 | 325226.658152191 | 0.035585 | 1720 | 1 | 39 | 4595 | 4676 | 5020 | 4941 | 4284
4 | 325226.723992678 | 325226.689280103 | 325226.694196138 | 325226.706421887 | 0.048227 | 1719 | 3 | 31 | 4532 | 4492 | 4960 | 5203 | 4561
5 | 325226.756035692 | 325226.726008457 | 325226.729061998 | 325226.745393227 | 0.038862 | 1720 | 1 | 32 | 4612 | 4757 | 4950 | 4216 | 4468
6 | 325226.795094683 | 325226.765851762 | 325226.762098261 | 325226.785735013 | 0.040268 | 1718 | 3 | 30 | 4738 | 4687 | 4066 | 5051 | 5281
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
