CaptainOrangeSparrow/early-fire-detection-classifier/data-recording/test_recordings/recording_test_25fps_2026-01-25_001_1769390880_19-28-00/adc.csv

frame_idx | t_sample_perf_counter | t_reg_frame | t_ir_frame | t_adc_sweep | adc_sweep_dt_s | adc0_ch0 | adc0_ch1 | adc0_ch2 | adc0_ch3 | adc1_ch0 | adc1_ch1 | adc1_ch2 | adc1_ch3
0 | 343239.506800773 | 343239.470828580 | 343239.461834268 | 343239.469288253 | 0.033821 | 1719 | 279 | 486 | 4751 | 4757 | 4666 | 4051 | 4890
1 | 343239.539034085 | 343239.506383322 | 343239.509915446 | 343239.514735890 | 0.045415 | 1723 | 278 | 410 | 4738 | 4763 | 4271 | 4651 | 4127
2 | 343239.569508984 | 343239.539097063 | 343239.543979557 | 343239.554854686 | 0.040085 | 1721 | 280 | 39 | 4671 | 4768 | 4619 | 4181 | 4990
3 | 343239.608969619 | 343239.570837115 | 343239.579270164 | 343239.593362400 | 0.038452 | 1719 | 280 | 140 | 4684 | 4630 | 4861 | 5132 | 4696
4 | 343239.647897408 | 343239.637706969 | 343239.618748816 | 343239.629890511 | 0.036487 | 1721 | 277 | 79 | 4654 | 4688 | 5104 | 4809 | 4313
5 | 343239.687948586 | 343239.669725876 | 343239.657442615 | 343239.677500284 | 0.047561 | 1722 | 282 | 44 | 4700 | 4640 | 4932 | 5121 | 4631
6 | 343239.726828758 | 343239.706168353 | 343239.698706112 | 343239.715915292 | 0.038382 | 1719 | 279 | 48 | 4686 | 4748 | 5067 | 4569 | 4187
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
