CaptainOrangeSparrow/early-fire-detection-classifier/data-recording/test_recordings/recording_test_25fps_2026-01-25_002_1769373397_14-36-37/adc.csv

frame_idx | t_sample_perf_counter | t_reg_frame | t_ir_frame | t_adc_sweep | adc_sweep_dt_s | adc0_ch0 | adc0_ch1 | adc0_ch2 | adc0_ch3 | adc1_ch0 | adc1_ch1 | adc1_ch2 | adc1_ch3
0 | 325757.098538744 | 325757.057674085 | 325757.042100374 | 325757.054962626 | 0.031653 | 1721 | 2 | 31 | 4728 | 4725 | 4023 | 4643 | 5093
1 | 325757.133939236 | 325757.098775044 | 325757.121558895 | 325757.100542937 | 0.045544 | 1720 | 1 | 30 | 4691 | 4745 | 4530 | 4232 | 4130
2 | 325757.160364447 | 325757.136995160 | 325757.121558895 | 325757.140613158 | 0.040041 | 1721 | 3 | 28 | 4620 | 4752 | 4911 | 4496 | 5154
3 | 325757.206863618 | 325757.176336578 | 325757.166127989 | 325757.180947680 | 0.040217 | 1719 | 3 | 36 | 4643 | 4708 | 5172 | 4705 | 4067
4 | 325757.238865482 | 325757.217100144 | 325757.211384124 | 325757.223823733 | 0.042851 | 1720 | 1 | 30 | 4677 | 4687 | 4002 | 4885 | 5238
5 | 325757.280255287 | 325757.256230384 | 325757.243177018 | 325757.259060697 | 0.035209 | 1718 | 4 | 35 | 4680 | 4611 | 4566 | 5159 | 4855
6 | 325757.319298579 | 325757.296493671 | 325757.285950506 | 325757.300435717 | 0.041335 | 1719 | 3 | 32 | 4533 | 4736 | 5160 | 4540 | 4130
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
