CaptainOrangeSparrow/early-fire-detection-classifier/data-recording/test_recordings/recording_test_25fps_2026-01-25_002_1769391107_19-31-47/adc.csv

frame_idx | t_sample_perf_counter | t_reg_frame | t_ir_frame | t_adc_sweep | adc_sweep_dt_s | adc0_ch0 | adc0_ch1 | adc0_ch2 | adc0_ch3 | adc1_ch0 | adc1_ch1 | adc1_ch2 | adc1_ch3
0 | 343466.688167068 | 343466.661081383 | 343466.641728705 | 343466.646371677 | 0.032217 | 1723 | 280 | 494 | 4729 | 4693 | 4204 | 4617 | 5078
1 | 343466.717429772 | 343466.694818095 | 343466.678454968 | 343466.696186515 | 0.049786 | 1728 | 281 | 459 | 4769 | 4702 | 4105 | 5574 | 5313
2 | 343466.754114723 | 343466.723447245 | 343466.718929972 | 343466.740466645 | 0.044245 | 1725 | 281 | 486 | 4749 | 4512 | 5159 | 4392 | 4349
3 | 343466.793271195 | 343466.759754810 | 343466.756187354 | 343466.775996621 | 0.035481 | 1725 | 279 | 511 | 4726 | 4806 | 4617 | 4234 | 4918
4 | 343466.832216718 | 343466.823616616 | 343466.797018720 | 343466.814938624 | 0.038886 | 1726 | 280 | 430 | 4740 | 4695 | 4042 | 5049 | 5021
5 | 343466.871582413 | 343466.859157536 | 343466.835850000 | 343466.852211686 | 0.037238 | 1726 | 280 | 347 | 4676 | 4689 | 4951 | 5077 | 4597
6 | 343466.912773596 | 343466.891371007 | 343466.875503190 | 343466.891927214 | 0.039656 | 1723 | 282 | 41 | 4708 | 4737 | 5221 | 4205 | 4790
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
