CaptainOrangeSparrow/early-fire-detection-classifier/data-recording/test_recordings/recording_test_25fps_2026-01-25_003_1769373421_14-37-01/adc.csv

frame_idx | t_sample_perf_counter | t_reg_frame | t_ir_frame | t_adc_sweep | adc_sweep_dt_s | adc0_ch0 | adc0_ch1 | adc0_ch2 | adc0_ch3 | adc1_ch0 | adc1_ch1 | adc1_ch2 | adc1_ch3
0 | 325781.100756827 | 325781.078217651 | 325781.083650012 | 325781.056852773 | 0.031007 | 1726 | 3 | 28 | 4597 | 4689 | 5158 | 4782 | 4231
1 | 325781.130293752 | 325781.118146217 | 325781.121887007 | 325781.104595862 | 0.047714 | 1723 | 3 | 31 | 4613 | 4636 | 5065 | 4072 | 4628
2 | 325781.170986450 | 325781.158073726 | 325781.121887007 | 325781.146086199 | 0.041448 | 1722 | 0 | 37 | 4595 | 4868 | 4661 | 4381 | 4961
3 | 325781.210044221 | 325781.197234895 | 325781.201637733 | 325781.185353165 | 0.039196 | 1722 | 0 | 22 | 4706 | 4594 | 4518 | 4969 | 4941
4 | 325781.248148602 | 325781.237278570 | 325781.241065378 | 325781.226489341 | 0.041070 | 1725 | 3 | 36 | 4653 | 4541 | 5119 | 4606 | 4237
5 | 325781.289714751 | 325781.277560176 | 325781.282047435 | 325781.265716944 | 0.039158 | 1725 | 0 | 27 | 4679 | 4733 | 3879 | 4817 | 5174
6 | 325781.330790669 | 325781.317205016 | 325781.321265341 | 325781.304587955 | 0.038813 | 1725 | -2 | 32 | 4730 | 4476 | 4970 | 5088 | 4586
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
