CaptainOrangeSparrow/early-fire-detection-classifier/data-recording/test_recordings/recording_test_25fps_2026-01-25_004_1769373480_14-38-00/adc.csv

frame_idx | t_sample_perf_counter | t_reg_frame | t_ir_frame | t_adc_sweep | adc_sweep_dt_s | adc0_ch0 | adc0_ch1 | adc0_ch2 | adc0_ch3 | adc1_ch0 | adc1_ch1 | adc1_ch2 | adc1_ch3
0 | 325839.700137645 | 325839.657885379 | 325839.640653871 | 325839.671121970 | 0.029017 | 1730 | 2 | 30 | 4645 | 4629 | 4922 | 5169 | 4795
1 | 325839.725140290 | 325839.700223474 | 325839.682752625 | 325839.671121970 | 0.029017 | 1730 | 2 | 30 | 4645 | 4629 | 4922 | 5169 | 4795
2 | 325839.756908134 | 325839.738179751 | 325839.720805388 | 325839.725448401 | 0.054299 | 1728 | 3 | 35 | 4660 | 4603 | 4509 | 5248 | 4576
3 | 325839.803684400 | 325839.778157761 | 325839.764743785 | 325839.763131802 | 0.037646 | 1728 | 1 | 32 | 4628 | 4628 | 5039 | 5080 | 4551
4 | 325839.836200888 | 325839.818726968 | 325839.804878059 | 325839.805607823 | 0.042353 | 1728 | -1 | 34 | 4711 | 4702 | 4265 | 4710 | 5487
5 | 325839.875927910 | 325839.858712466 | 325839.849257470 | 325839.846216360 | 0.040545 | 1731 | 3 | 35 | 4664 | 4584 | 4545 | 5251 | 3888
6 | 325839.921039485 | 325839.898118864 | 325839.882723766 | 325839.883662340 | 0.037302 | 1730 | 0 | 28 | 4697 | 4786 | 4844 | 4188 | 5238
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
