CaptainOrangeSparrow/early-fire-detection-classifier/data-recording/test_recordings/recording_test_25fps_2026-01-25_005_1769373503_14-38-23/adc.csv

frame_idx | t_sample_perf_counter | t_reg_frame | t_ir_frame | t_adc_sweep | adc_sweep_dt_s | adc0_ch0 | adc0_ch1 | adc0_ch2 | adc0_ch3 | adc1_ch0 | adc1_ch1 | adc1_ch2 | adc1_ch3
0 | 325862.440161394 | 325862.412444495 | 325862.401250145 | 325862.391444697 | 0.034661 | 1729 | 2 | 24 | 4648 | 4788 | 4821 | 4259 | 4612
1 | 325862.467741039 | 325862.449936409 | 325862.446704248 | 325862.440866133 | 0.049390 | 1728 | 0 | 27 | 4644 | 4740 | 4961 | 4844 | 5387
2 | 325862.500525583 | 325862.489824891 | 325862.475220164 | 325862.480658610 | 0.039690 | 1728 | 0 | 25 | 4672 | 4833 | 4094 | 4813 | 5166
3 | 325862.541249659 | 325862.529811361 | 325862.523772885 | 325862.523903771 | 0.043212 | 1726 | 0 | 34 | 4721 | 4598 | 4585 | 5402 | 4230
4 | 325862.578919662 | 325862.569792199 | 325862.555765005 | 325862.562961299 | 0.039036 | 1728 | 1 | 31 | 4704 | 4746 | 4176 | 4606 | 5165
5 | 325862.624825659 | 325862.610328169 | 325862.596201034 | 325862.604790198 | 0.041792 | 1730 | -1 | 34 | 4691 | 4606 | 4514 | 5491 | 4630
6 | 325862.660452393 | 325862.650122790 | 325862.637959017 | 325862.653003222 | 0.048166 | 1726 | 1 | 36 | 4656 | 4616 | 4953 | 5145 | 4510
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
