CaptainOrangeSparrow/early-fire-detection-classifier/data-recording/test_recordings/recording_test_25fps_2026-01-25_006_1769374208_14-50-08/adc.csv

frame_idx | t_sample_perf_counter | t_reg_frame | t_ir_frame | t_adc_sweep | adc_sweep_dt_s | adc0_ch0 | adc0_ch1 | adc0_ch2 | adc0_ch3 | adc1_ch0 | adc1_ch1 | adc1_ch2 | adc1_ch3
0 | 326567.407796735 | 326567.377117101 | 326567.353018564 | 326567.361622555 | 0.032455 | 1684 | 1 | 27 | 4646 | 4771 | 4861 | 4521 | 4325
1 | 326567.440140492 | 326567.416471418 | 326567.396943084 | 326567.408042188 | 0.046393 | 1683 | 7 | 32 | 4608 | 4758 | 5208 | 4626 | 4597
2 | 326567.468833489 | 326567.456037683 | 326567.443055083 | 326567.452367146 | 0.044208 | 1681 | 2 | 34 | 4665 | 4617 | 5282 | 4677 | 5239
3 | 326567.512265182 | 326567.494797408 | 326567.475023748 | 326567.489509502 | 0.037074 | 1682 | -1 | 36 | 4629 | 4607 | 4872 | 5149 | 4654
4 | 326567.550007475 | 326567.534807953 | 326567.518063163 | 326567.531645828 | 0.042094 | 1683 | 1 | 35 | 4639 | 4769 | 4696 | 3991 | 4860
5 | 326567.589002156 | 326567.574821859 | 326567.557113048 | 326567.571065045 | 0.039376 | 1685 | 2 | 26 | 4682 | 4685 | 4455 | 4980 | 4992
6 | 326567.630552146 | 326567.614807379 | 326567.596331070 | 326567.608402260 | 0.037287 | 1683 | 2 | 36 | 4569 | 4633 | 5119 | 4876 | 4401
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
