CaptainOrangeSparrow/early-fire-detection-classifier/data-recording/test_recordings/recording_test_25fps_2026-01-25_007_1769375159_15-05-59/adc.csv

frame_idx | t_sample_perf_counter | t_reg_frame | t_ir_frame | t_adc_sweep | adc_sweep_dt_s | adc0_ch0 | adc0_ch1 | adc0_ch2 | adc0_ch3 | adc1_ch0 | adc1_ch1 | adc1_ch2 | adc1_ch3
0 | 327518.952428320 | 327518.915993054 | 327518.913553854 | 327518.938701259 | 0.037569 | 1675 | 4 | 33 | 4721 | 4695 | 4171 | 4877 | 5174
1 | 327518.983856928 | 327518.957845352 | 327518.958604050 | 327518.938701259 | 0.037569 | 1675 | 4 | 33 | 4721 | 4695 | 4171 | 4877 | 5174
2 | 327519.020189024 | 327518.995822046 | 327518.991931242 | 327518.991256289 | 0.052514 | 1676 | 2 | 25 | 4726 | 4805 | 4659 | 4809 | 5029
3 | 327519.061397121 | 327519.035189542 | 327519.032980297 | 327519.026067918 | 0.034759 | 1675 | 3 | 42 | 4673 | 4607 | 4489 | 5628 | 4647
4 | 327519.100664106 | 327519.076153765 | 327519.072265969 | 327519.065189267 | 0.039019 | 1676 | 3 | 37 | 4640 | 4621 | 4910 | 5230 | 4055
5 | 327519.139591470 | 327519.115035016 | 327519.112544711 | 327519.111438009 | 0.046155 | 1675 | 1 | 37 | 4722 | 4648 | 4788 | 4881 | 4280
6 | 327519.180971603 | 327519.157747231 | 327519.159015088 | 327519.153018720 | 0.041547 | 1677 | 1 | 34 | 4646 | 4618 | 4999 | 4532 | 4523
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
