CaptainOrangeSparrow/early-fire-detection-classifier/data-recording/test_recordings/recording_test_25fps_2026-01-25_008_1769375182_15-06-22/adc.csv

frame_idx | t_sample_perf_counter | t_reg_frame | t_ir_frame | t_adc_sweep | adc_sweep_dt_s | adc0_ch0 | adc0_ch1 | adc0_ch2 | adc0_ch3 | adc1_ch0 | adc1_ch1 | adc1_ch2 | adc1_ch3
0 | 327541.535821854 | 327541.499817438 | 327541.516210087 | 327541.494244271 | 0.030642 | 1680 | 0 | 30 | 4637 | 4702 | 5034 | 4905 | 4350
1 | 327541.576394464 | 327541.539732310 | 327541.551455645 | 327541.526030067 | 0.031774 | 1678 | 1 | 34 | 4664 | 4635 | 4939 | 5172 | 4558
2 | 327541.608325766 | 327541.580531195 | 327541.592812810 | 327541.570445227 | 0.044379 | 1679 | 0 | 24 | 4694 | 4790 | 4510 | 4287 | 5307
3 | 327541.643960257 | 327541.620050637 | 327541.633921235 | 327541.617219429 | 0.046727 | 1679 | 2 | 37 | 4626 | 4633 | 5292 | 4049 | 4820
4 | 327541.683470996 | 327541.659872100 | 327541.671006754 | 327541.657435105 | 0.040163 | 1679 | 1 | 34 | 4729 | 4515 | 4774 | 5164 | 4815
5 | 327541.725757901 | 327541.701000813 | 327541.711226495 | 327541.693539107 | 0.036054 | 1678 | 2 | 37 | 4673 | 4595 | 4994 | 4991 | 4528
6 | 327541.762253557 | 327541.739883318 | 327541.751064790 | 327541.733836768 | 0.040249 | 1676 | 0 | 30 | 4595 | 4694 | 5228 | 4004 | 4886
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
