CaptainOrangeSparrow/early-fire-detection-classifier/data-recording/test_recordings/recording_test_25fps_2026-01-25_009_1769375408_15-10-08/adc.csv

frame_idx | t_sample_perf_counter | t_reg_frame | t_ir_frame | t_adc_sweep | adc_sweep_dt_s | adc0_ch0 | adc0_ch1 | adc0_ch2 | adc0_ch3 | adc1_ch0 | adc1_ch1 | adc1_ch2 | adc1_ch3
0 | 327767.777326677 | 327767.741004947 | 327767.733156774 | 327767.743127618 | 0.031643 | 1684 | 1 | 29 | 4655 | 4657 | 5267 | 4834 | 4420
1 | 327767.805287614 | 327767.781618964 | 327767.791424268 | 327767.798007582 | 0.054864 | 1684 | 2 | 31 | 4658 | 4504 | 5066 | 4209 | 4573
2 | 327767.836185481 | 327767.820720531 | 327767.812461245 | 327767.798007582 | 0.054864 | 1684 | 2 | 31 | 4658 | 4504 | 5066 | 4209 | 4573
3 | 327767.883932135 | 327767.860621892 | 327767.849924856 | 327767.873357501 | 0.035236 | 1683 | 1 | 38 | 4717 | 4628 | 4613 | 5127 | 4858
4 | 327767.916607416 | 327767.900813212 | 327767.890279251 | 327767.873357501 | 0.035236 | 1683 | 1 | 38 | 4717 | 4628 | 4613 | 5127 | 4858
5 | 327767.957113079 | 327767.940403142 | 327767.929622232 | 327767.918577380 | 0.045169 | 1681 | 3 | 26 | 4717 | 4808 | 4719 | 4054 | 5388
6 | 327768.000763803 | 327767.981262892 | 327767.969709837 | 327767.989863882 | 0.032106 | 1683 | 1 | 34 | 4697 | 4608 | 4558 | 5162 | 4836
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
