CaptainOrangeSparrow/early-fire-detection-classifier/data-recording/test_recordings/recording_test_25fps_2026-01-25_010_1769375531_15-12-11/adc.csv

frame_idx | t_sample_perf_counter | t_reg_frame | t_ir_frame | t_adc_sweep | adc_sweep_dt_s | adc0_ch0 | adc0_ch1 | adc0_ch2 | adc0_ch3 | adc1_ch0 | adc1_ch1 | adc1_ch2 | adc1_ch3
0 | 327890.348672971 | 327890.314364078 | 327890.322523803 | 327890.320619979 | 0.035739 | 1681 | 0 | 41 | 4705 | 4614 | 4519 | 4926 | 4392
1 | 327890.384796950 | 327890.355412884 | 327890.372439008 | 327890.366939094 | 0.046293 | 1681 | 2 | 25 | 4602 | 4857 | 4214 | 4932 | 4875
2 | 327890.420182862 | 327890.394754416 | 327890.399893457 | 327890.410065296 | 0.043073 | 1681 | 1 | 24 | 4648 | 4774 | 4904 | 3989 | 4861
3 | 327890.460535491 | 327890.434922176 | 327890.441579591 | 327890.450717420 | 0.040607 | 1683 | 3 | 33 | 4717 | 4722 | 4938 | 5186 | 4734
4 | 327890.499118731 | 327890.475404184 | 327890.480132207 | 327890.450717420 | 0.040607 | 1683 | 3 | 33 | 4717 | 4722 | 4938 | 5186 | 4734
5 | 327890.539436479 | 327890.514307177 | 327890.520182524 | 327890.532938940 | 0.033440 | 1683 | 0 | 34 | 4704 | 4672 | 4370 | 4977 | 4949
6 | 327890.582074765 | 327890.558553503 | 327890.569841050 | 327890.532938940 | 0.033440 | 1683 | 0 | 34 | 4704 | 4672 | 4370 | 4977 | 4949
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
