CaptainOrangeSparrow/early-fire-detection-classifier/data-recording/test_recordings/recording_test_25fps_2026-01-25_011_1769375552_15-12-32/adc.csv

frame_idx | t_sample_perf_counter | t_reg_frame | t_ir_frame | t_adc_sweep | adc_sweep_dt_s | adc0_ch0 | adc0_ch1 | adc0_ch2 | adc0_ch3 | adc1_ch0 | adc1_ch1 | adc1_ch2 | adc1_ch3
0 | 327911.294273801 | 327911.256144443 | 327911.242519999 | 327911.273136397 | 0.029581 | 1685 | 4 | 37 | 4682 | 4582 | 4704 | 5035 | 4931
1 | 327911.329538958 | 327911.297874565 | 327911.317611037 | 327911.273136397 | 0.029581 | 1685 | 4 | 37 | 4682 | 4582 | 4704 | 5035 | 4931
2 | 327911.358099687 | 327911.335973170 | 327911.317611037 | 327911.329665265 | 0.056507 | 1681 | 0 | 28 | 4717 | 4787 | 4715 | 4355 | 5224
3 | 327911.400462913 | 327911.376393883 | 327911.362283090 | 327911.367634267 | 0.037936 | 1685 | 1 | 27 | 4601 | 4686 | 5214 | 3939 | 4954
4 | 327911.436725120 | 327911.417600663 | 327911.411920326 | 327911.412689594 | 0.044974 | 1685 | 2 | 31 | 4713 | 4775 | 4569 | 5238 | 3964
5 | 327911.475620962 | 327911.456131216 | 327911.444692523 | 327911.450020372 | 0.037278 | 1684 | 0 | 30 | 4615 | 4678 | 5481 | 4169 | 4784
6 | 327911.519004246 | 327911.497150824 | 327911.482089927 | 327911.490135572 | 0.040039 | 1685 | 2 | 22 | 4699 | 4772 | 3866 | 5005 | 5047
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
