CaptainOrangeSparrow/early-fire-detection-classifier/data-recording/test_recordings/recording_test_25fps_2026-01-25_012_1769375564_15-12-44/adc.csv

frame_idx | t_sample_perf_counter | t_reg_frame | t_ir_frame | t_adc_sweep | adc_sweep_dt_s | adc0_ch0 | adc0_ch1 | adc0_ch2 | adc0_ch3 | adc1_ch0 | adc1_ch1 | adc1_ch2 | adc1_ch3
0 | 327923.915172582 | 327923.885821841 | 327923.881780329 | 327923.892381178 | 0.034062 | 1684 | 1 | 32 | 4714 | 4713 | 3910 | 4882 | 5313
1 | 327923.943897899 | 327923.926270148 | 327923.924974467 | 327923.892381178 | 0.034062 | 1684 | 1 | 32 | 4714 | 4713 | 3910 | 4882 | 5313
2 | 327923.979681158 | 327923.965894370 | 327923.957214498 | 327923.974539329 | 0.034906 | 1684 | -1 | 33 | 4752 | 4703 | 4101 | 4751 | 5177
3 | 327924.021094386 | 327924.006115312 | 327923.998067200 | 327924.009265217 | 0.034694 | 1683 | 2 | 35 | 4731 | 4710 | 4118 | 4694 | 5466
4 | 327924.059075398 | 327924.046311356 | 327924.038496339 | 327924.009265217 | 0.034694 | 1683 | 2 | 35 | 4731 | 4710 | 4118 | 4694 | 5466
5 | 327924.099359126 | 327924.085997213 | 327924.077617636 | 327924.059156328 | 0.049830 | 1682 | 2 | 31 | 4624 | 4781 | 4797 | 4116 | 5221
6 | 327924.141033001 | 327924.126265964 | 327924.125784928 | 327924.095505938 | 0.036312 | 1682 | 1 | 32 | 4709 | 4637 | 4392 | 5021 | 4901
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
