CaptainOrangeSparrow/early-fire-detection-classifier/data-recording/test_recordings/recording_test_25fps_2026-01-26_004_1769471776_17-56-16/adc.csv

frame_idx | t_sample_perf_counter | t_reg_frame | t_ir_frame | t_adc_sweep | adc_sweep_dt_s | adc0_ch0 | adc0_ch1 | adc0_ch2 | adc0_ch3 | adc1_ch0 | adc1_ch1 | adc1_ch2 | adc1_ch3 | ir_min | ir_max | ir_avg | ir_center
0 | 424136.465955393 | 424136.437954706 | 424136.457738459 | 424136.443067713 | 0.030621 | 1718 | 288 | 179 | 4710 | 4763 | 5006 | 4623 | 4171 | 27.412500000000023 | 36.85000000000002 | 30.909561411539755 | 32.35000000000002
1 | 424136.507585197 | 424136.473956385 | 424136.498481166 | 424136.443067713 | 0.030621 | 1718 | 288 | 179 | 4710 | 4763 | 5006 | 4623 | 4171 | 27.412500000000023 | 36.85000000000002 | 30.912981923421228 | 32.35000000000002
2 | 424136.536322224 | 424136.507819188 | 424136.498481166 | 424136.502186742 | 0.059080 | 1717 | 287 | 251 | 4720 | 4599 | 4747 | 5124 | 4488 | 27.412500000000023 | 36.85000000000002 | 30.912981923421228 | 32.35000000000002
3 | 424136.574698241 | 424136.536932482 | 424136.540483749 | 424136.545715063 | 0.043471 | 1715 | 287 | 185 | 4696 | 4600 | 5703 | 4273 | 4574 | 27.412500000000023 | 36.85000000000002 | 30.91539662679037 | 32.35000000000002
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
