CaptainOrangeSparrow/early-fire-detection-classifier/data-recording/test_recordings/recording_test_fps25_1769057509_001/adc.csv

frame_idx | t_sample_perf_counter | t_reg_frame | t_ir_frame | t_adc_sweep | adc_sweep_dt_s | adc0_ch0 | adc0_ch1 | adc0_ch2 | adc0_ch3 | adc1_ch0 | adc1_ch1 | adc1_ch2 | adc1_ch3
0 | 9868.063888711 | 9868.040322842 | 9868.041744340 | 9868.046597964 | 0.003679 | 4711 | 4711 | 1957 | 1957 | 5592 | 5592 | 5592 | 4668
1 | 9868.111538538 | 9868.080368531 | 9868.081631850 | 9868.100808263 | 0.003888 | 4664 | 4664 | 1956 | 1956 | 4728 | 4728 | 4728 | 4550
2 | 9868.146382660 | 9868.120890804 | 9868.120598031 | 9868.139088704 | 0.004193 | 4605 | 4605 | 4605 | 1958 | 4421 | 4586 | 4586 | 4586
3 | 9868.179592001 | 9868.159605941 | 9868.158678084 | 9868.167471140 | 0.003893 | 4684 | 4684 | 4684 | 1958 | 4726 | 4726 | 4726 | 4538
4 | 9868.208235562 | 9868.199725935 | 9868.197931599 | 9868.201502096 | 0.004317 | -102 | -102 | -102 | 1958 | 4848 | 4848 | 4848 | 4423
5 | 9868.248672234 | 9868.239597861 | 9868.236723185 | 9868.241497064 | 0.003733 | 4518 | 4518 | 4518 | 1954 | 4653 | 4653 | 4799 | 4799
6 | 9868.288800965 | 9868.279539868 | 9868.277060431 | 9868.281775685 | 0.003734 | 4730 | 4730 | 1956 | 1956 | 5887 | 5887 | 5887 | 4572
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
