CaptainOrangeSparrow/early-fire-detection-classifier/data-recording/test_recordings/recording_test_fps25_1769057681_001/adc.csv

frame_idx | t_sample_perf_counter | t_reg_frame | t_ir_frame | t_adc_sweep | adc_sweep_dt_s | adc0_ch0 | adc0_ch1 | adc0_ch2 | adc0_ch3 | adc1_ch0 | adc1_ch1 | adc1_ch2 | adc1_ch3
0 | 10040.610715948 | 10040.573687318 | 10040.580333619 | 10040.599477881 | 0.003384 | 4601 | 4601 | 4601 | 1955 | 4170 | 4170 | 4170 | 4575
1 | 10040.661894378 | 10040.612545646 | 10040.620958091 | 10040.642778116 | 0.003721 | 4686 | 4686 | 1957 | 1957 | 5419 | 5419 | 5419 | 4751
2 | 10040.719267708 | 10040.692512391 | 10040.702083866 | 10040.706117734 | 0.012167 | -106 | 1955 | 135 | 135 | 5731 | 5731 | 5731 | 4594
3 | 10040.763562617 | 10040.731491649 | 10040.739730811 | 10040.752061538 | 0.003617 | 4564 | 4564 | 4564 | 1956 | 3837 | 3837 | 3837 | 4666
4 | 10040.805947347 | 10040.772941289 | 10040.784712517 | 10040.793708301 | 0.003811 | 4738 | 4738 | 1954 | 1954 | 5671 | 5671 | 5671 | 4695
5 | 10041.004973025 | 10040.971738866 | 10040.983281386 | 10040.990057097 | 0.005292 | 4691 | 4691 | 4691 | 1951 | 4186 | 4186 | 4847 | 4847
6 | 10041.241120646 | 10041.211544924 | 10041.221450614 | 10041.214487283 | 0.003654 | 4672 | 4672 | 1954 | 1954 | 4712 | 4712 | 4712 | 4555
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
