CaptainOrangeSparrow/early-fire-detection-classifier/data-recording/test_recordings/recording_testagain_25fps_2026-01-25_001_1769388568_18-49-28/adc.csv

frame_idx | t_sample_perf_counter | t_reg_frame | t_ir_frame | t_adc_sweep | adc_sweep_dt_s | adc0_ch0 | adc0_ch1 | adc0_ch2 | adc0_ch3 | adc1_ch0 | adc1_ch1 | adc1_ch2 | adc1_ch3
0 | 340927.407784633 | 340927.375492408 | 340927.383344410 | 340927.392886029 | 0.034754 | 1713 | 281 | 387 | 4767 | 4670 | 4072 | 5046 | 4880
1 | 340927.445062505 | 340927.407112198 | 340927.413463164 | 340927.392886029 | 0.034754 | 1713 | 281 | 387 | 4767 | 4670 | 4072 | 5046 | 4880
2 | 340927.482169812 | 340927.440860176 | 340927.453607327 | 340927.441549732 | 0.048630 | 1713 | 279 | 491 | 4766 | 4771 | 4624 | 4077 | 5491
3 | 340927.516534992 | 340927.504716733 | 340927.493953639 | 340927.484926595 | 0.043342 | 1713 | 279 | 112 | 4696 | 4613 | 4795 | 5151 | 4305
4 | 340927.557277700 | 340927.541687460 | 340927.534854175 | 340927.527184739 | 0.042175 | 1712 | 280 | 507 | 4749 | 4760 | 4212 | 5125 | 4844
5 | 340927.596365064 | 340927.572683039 | 340927.573539704 | 340927.571465148 | 0.044170 | 1713 | 278 | 127 | 4685 | 4784 | 4640 | 4200 | 4944
6 | 340927.642175470 | 340927.604800667 | 340927.612809569 | 340927.611444186 | 0.039928 | 1714 | 281 | 532 | 4757 | 4730 | 4606 | 5120 | 4786
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
