CaptainOrangeSparrow/early-fire-detection-classifier/data-recording/test_recordings/recording_testagain_25fps_2026-01-25_002_1769388733_18-52-13/adc.csv

frame_idx | t_sample_perf_counter | t_reg_frame | t_ir_frame | t_adc_sweep | adc_sweep_dt_s | adc0_ch0 | adc0_ch1 | adc0_ch2 | adc0_ch3 | adc1_ch0 | adc1_ch1 | adc1_ch2 | adc1_ch3
0 | 341093.218800858 | 341093.174119596 | 341093.205949537 | 341093.190591576 | 0.031282 | 1717 | 281 | 359 | 4749 | 4662 | 4251 | 4917 | 5073
1 | 341093.252526219 | 341093.242907065 | 341093.205949537 | 341093.237764789 | 0.047151 | 1718 | 278 | 184 | 4673 | 4777 | 4595 | 4219 | 5033
2 | 341093.284410530 | 341093.271323073 | 341093.247620719 | 341093.237764789 | 0.047151 | 1718 | 278 | 184 | 4673 | 4777 | 4595 | 4219 | 5033
3 | 341093.324350489 | 341093.307279801 | 341093.280144922 | 341093.316415196 | 0.032251 | 1715 | 279 | 88 | 4672 | 4738 | 4918 | 4579 | 4398
4 | 341093.363121291 | 341093.340392535 | 341093.325066480 | 341093.316415196 | 0.032251 | 1715 | 279 | 88 | 4672 | 4738 | 4918 | 4579 | 4398
5 | 341093.405847258 | 341093.373721852 | 341093.363751455 | 341093.363547096 | 0.047096 | 1716 | 281 | 316 | 4722 | 4633 | 4629 | 4954 | 4902
6 | 341093.447796049 | 341093.411354506 | 341093.440447848 | 341093.406060545 | 0.042459 | 1715 | 280 | 162 | 4691 | 4776 | 4913 | 4539 | 4364
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
