CaptainOrangeSparrow/early-fire-detection-classifier/hw/KiCAD/Paper_Prints/print6-104.pdf

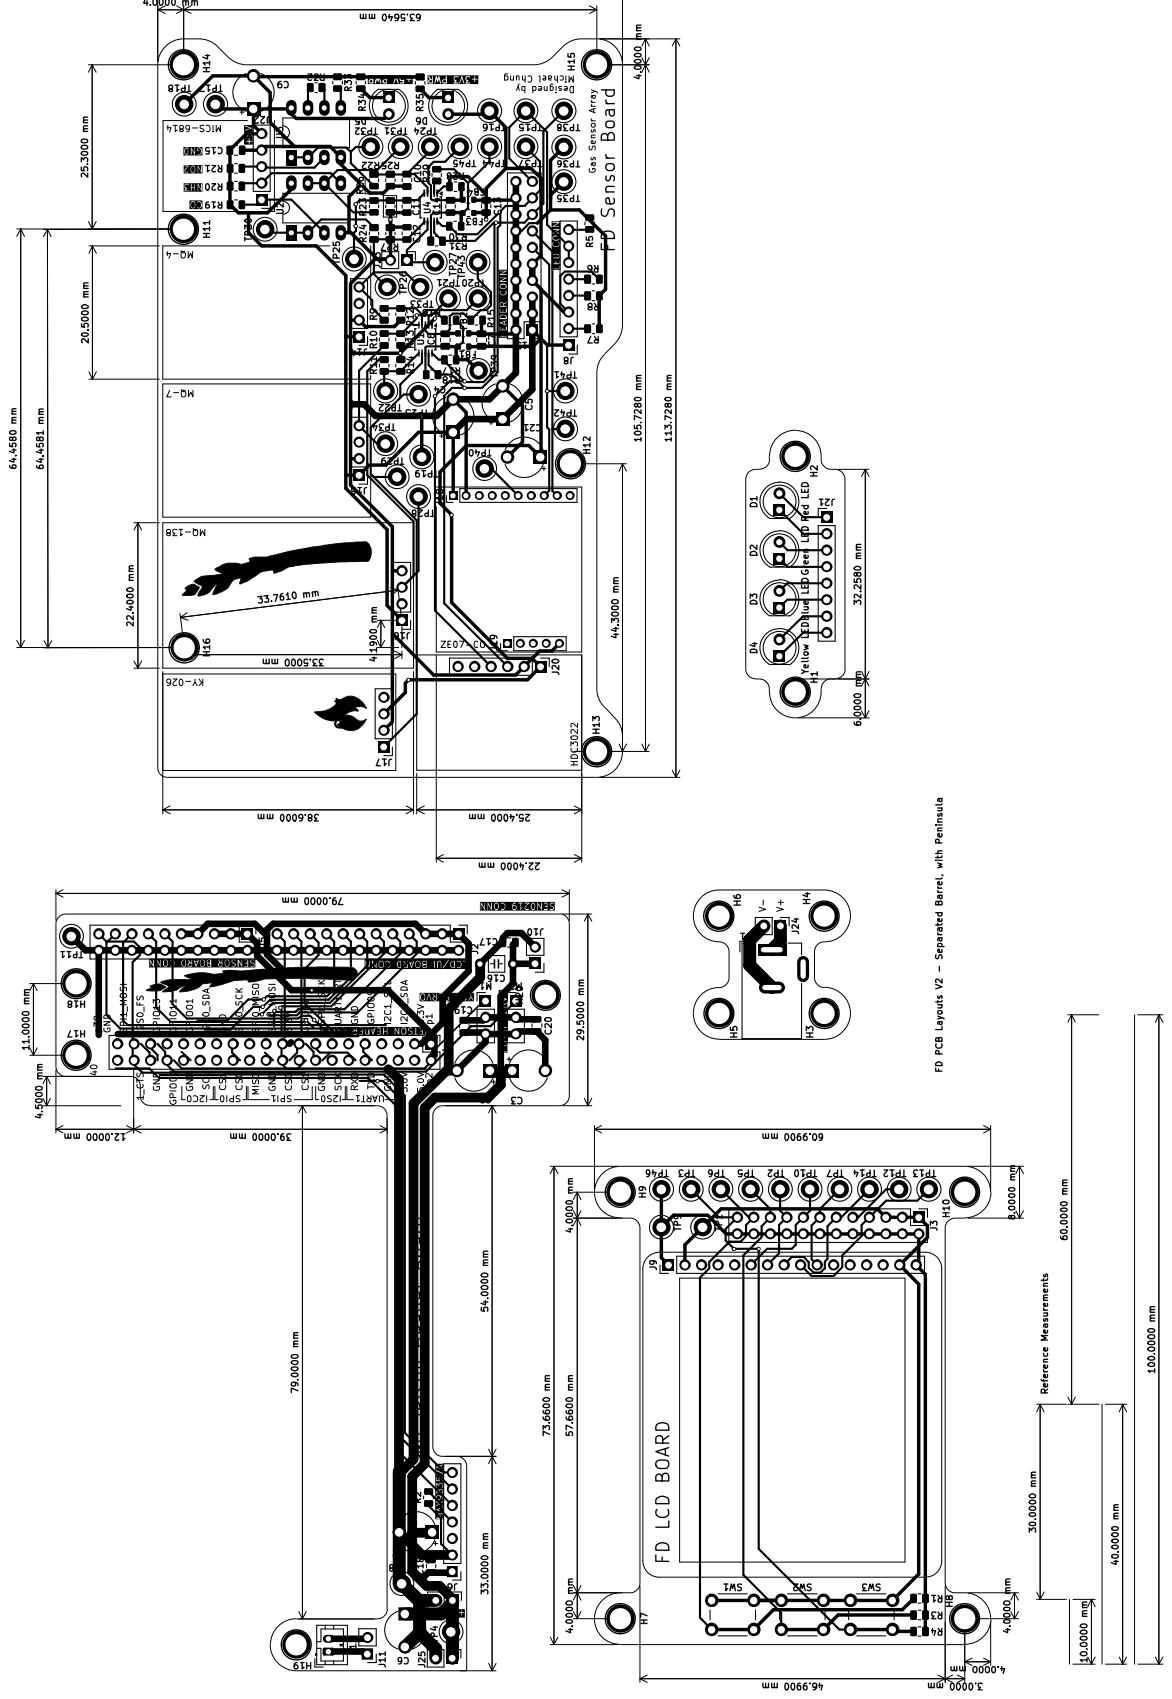
[picture p17: page 1]
