CaptainOrangeSparrow/early-fire-detection-classifier/hw/KiCAD/Paper_Prints/print6.pdf

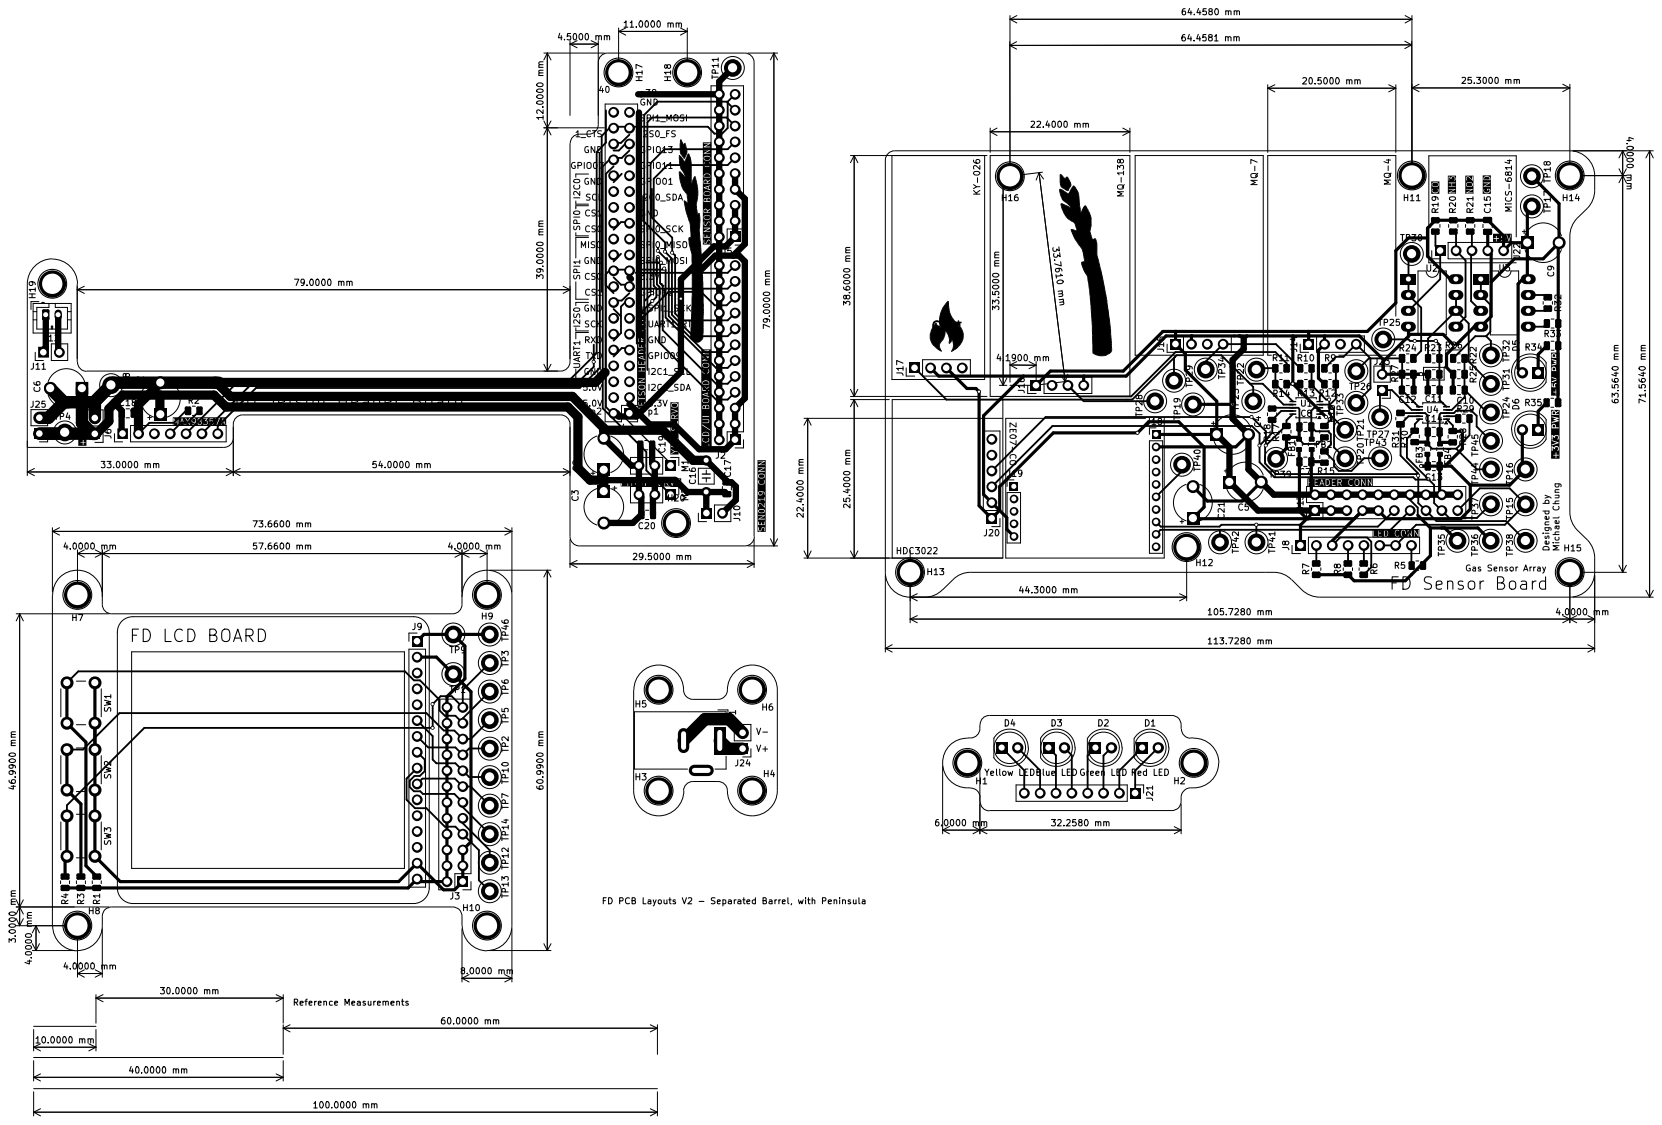
[picture p18: page 1]
