CaptainOrangeSparrow/early-fire-detection-classifier/hw/KiCAD/Paper_Prints/print7-104.pdf

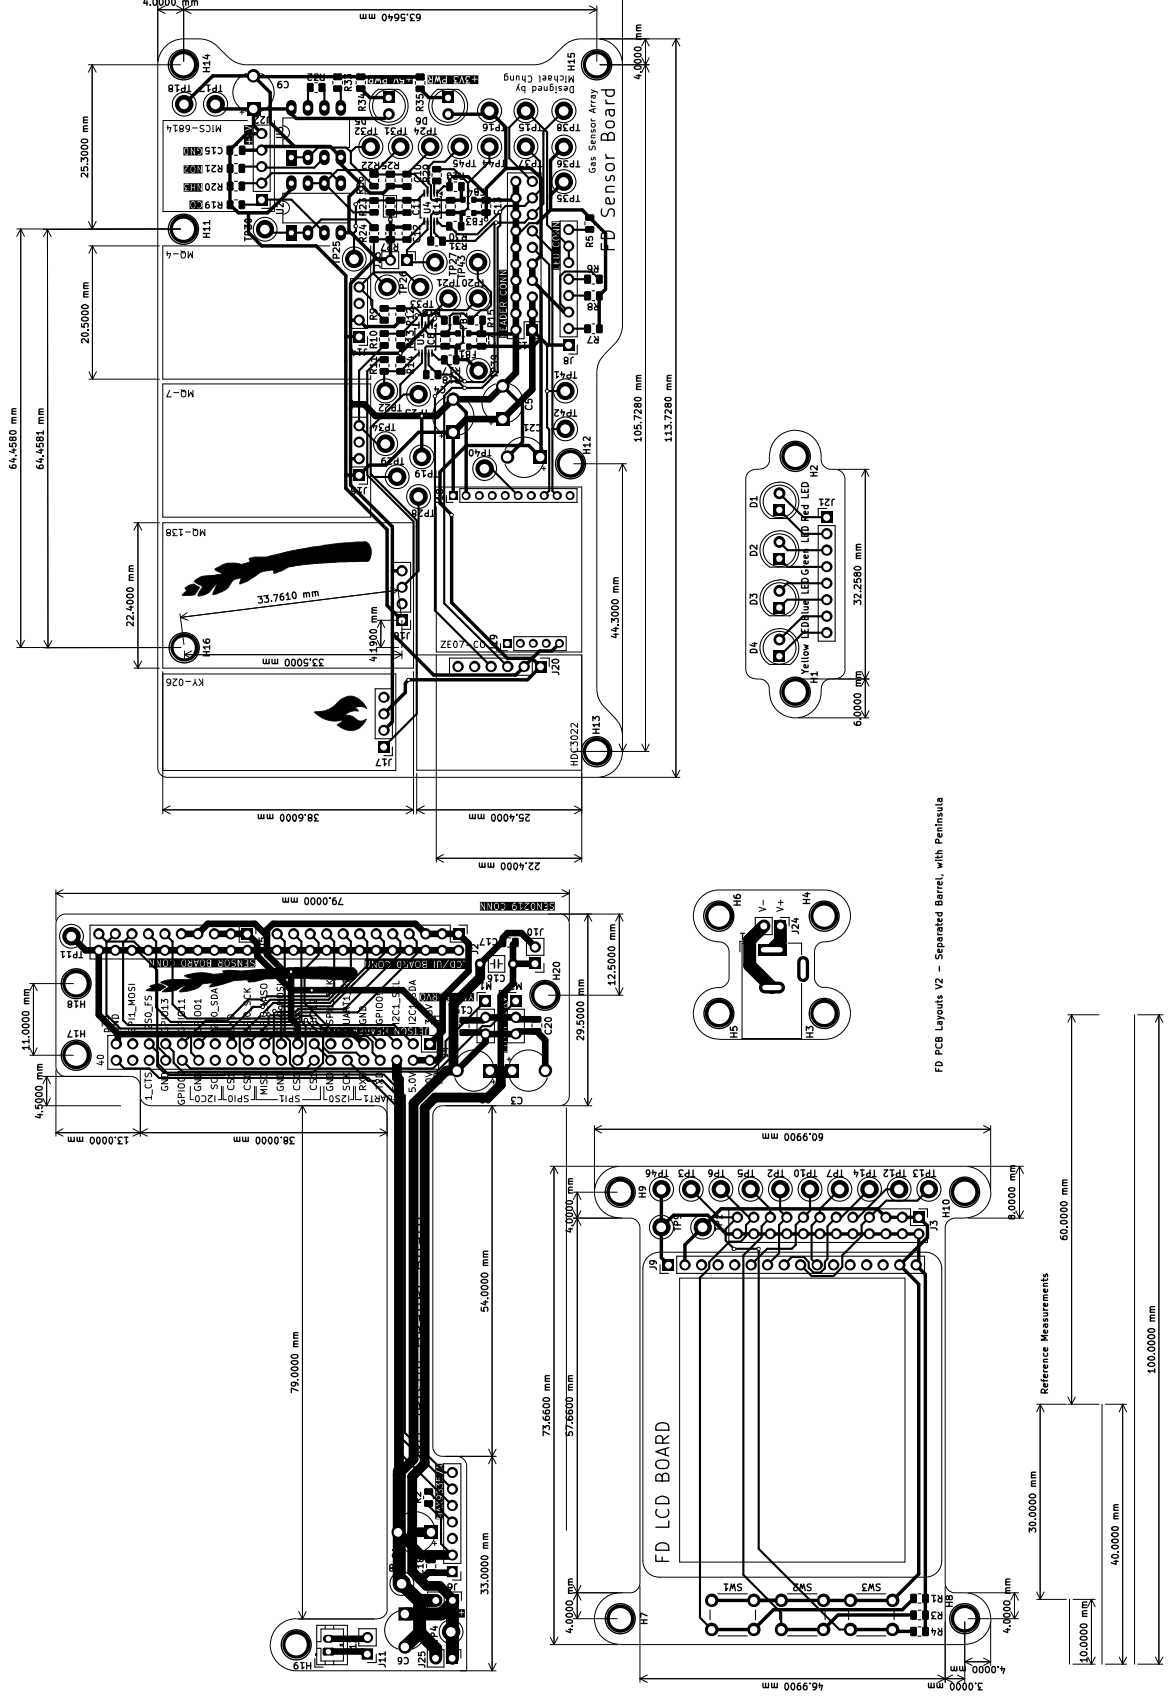
[picture p19: page 1]
