CaptainOrangeSparrow/early-fire-detection-classifier/hw/KiCAD/Paper_Prints/print7.pdf

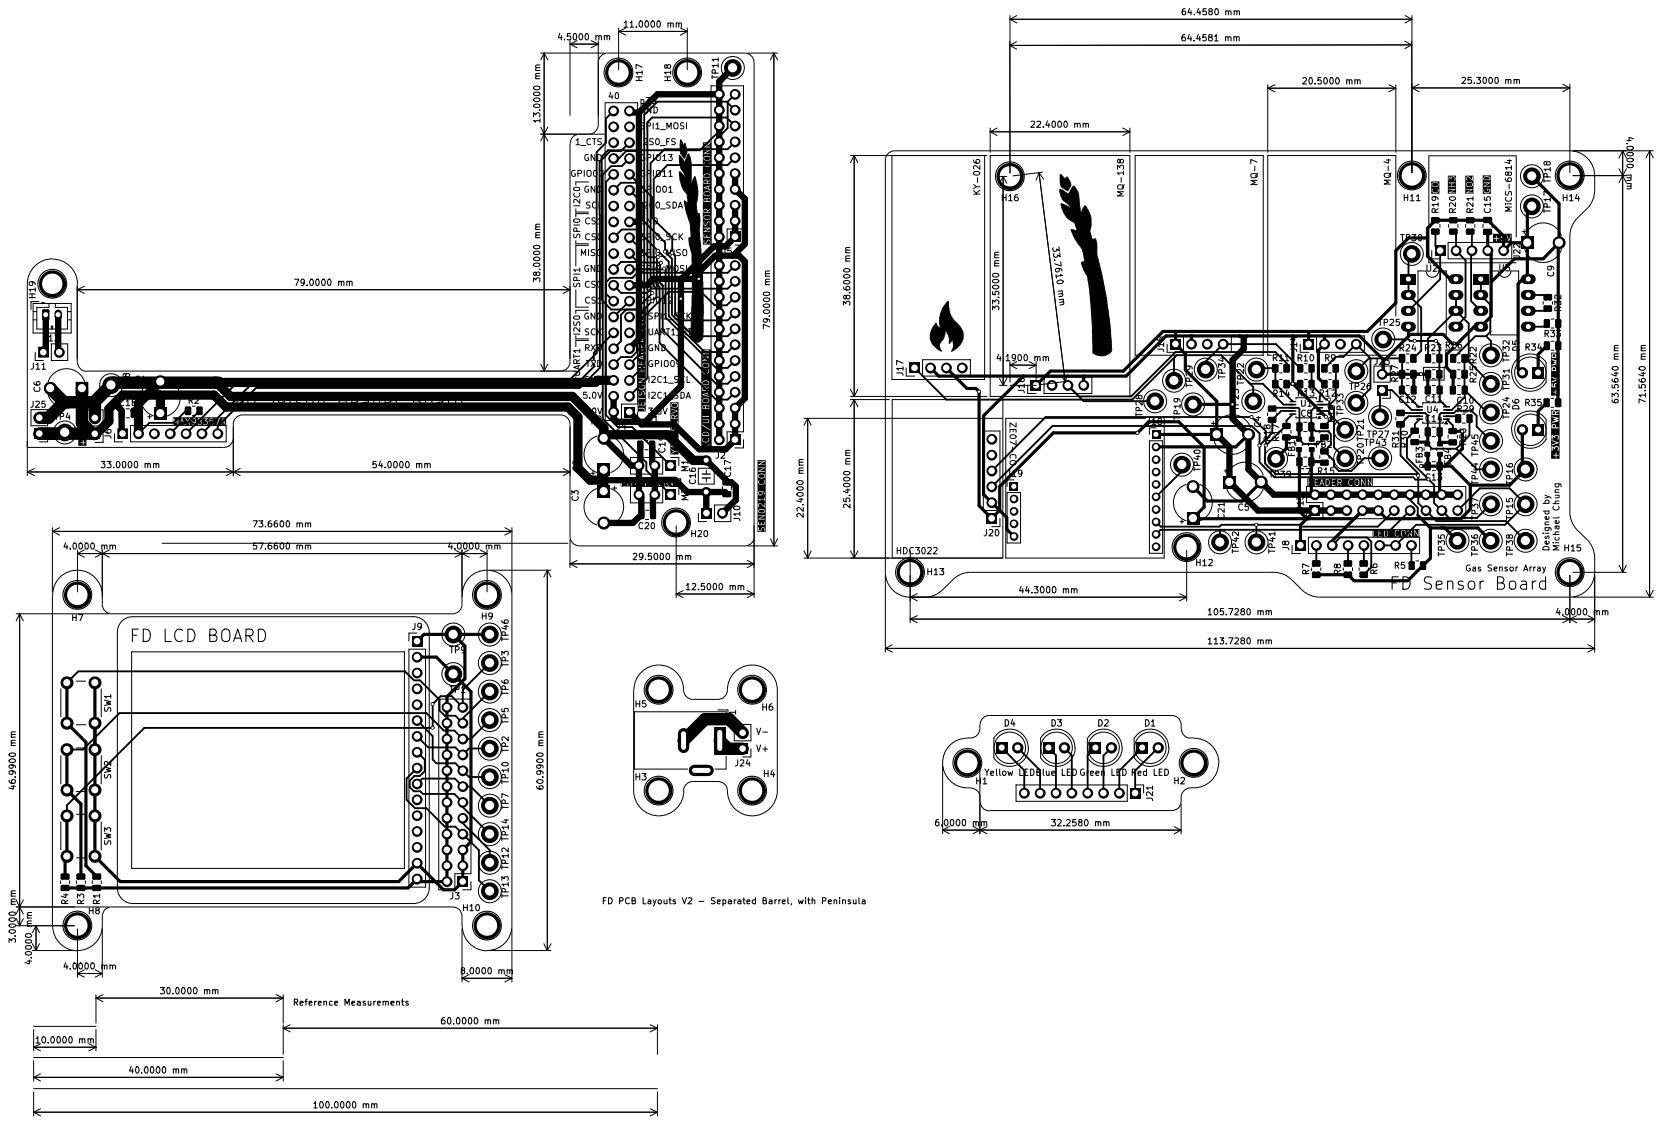
[picture p20: page 1]
