CaptainOrangeSparrow/early-fire-detection-classifier/hw/KiCAD/Paper_Prints/print8-104.pdf

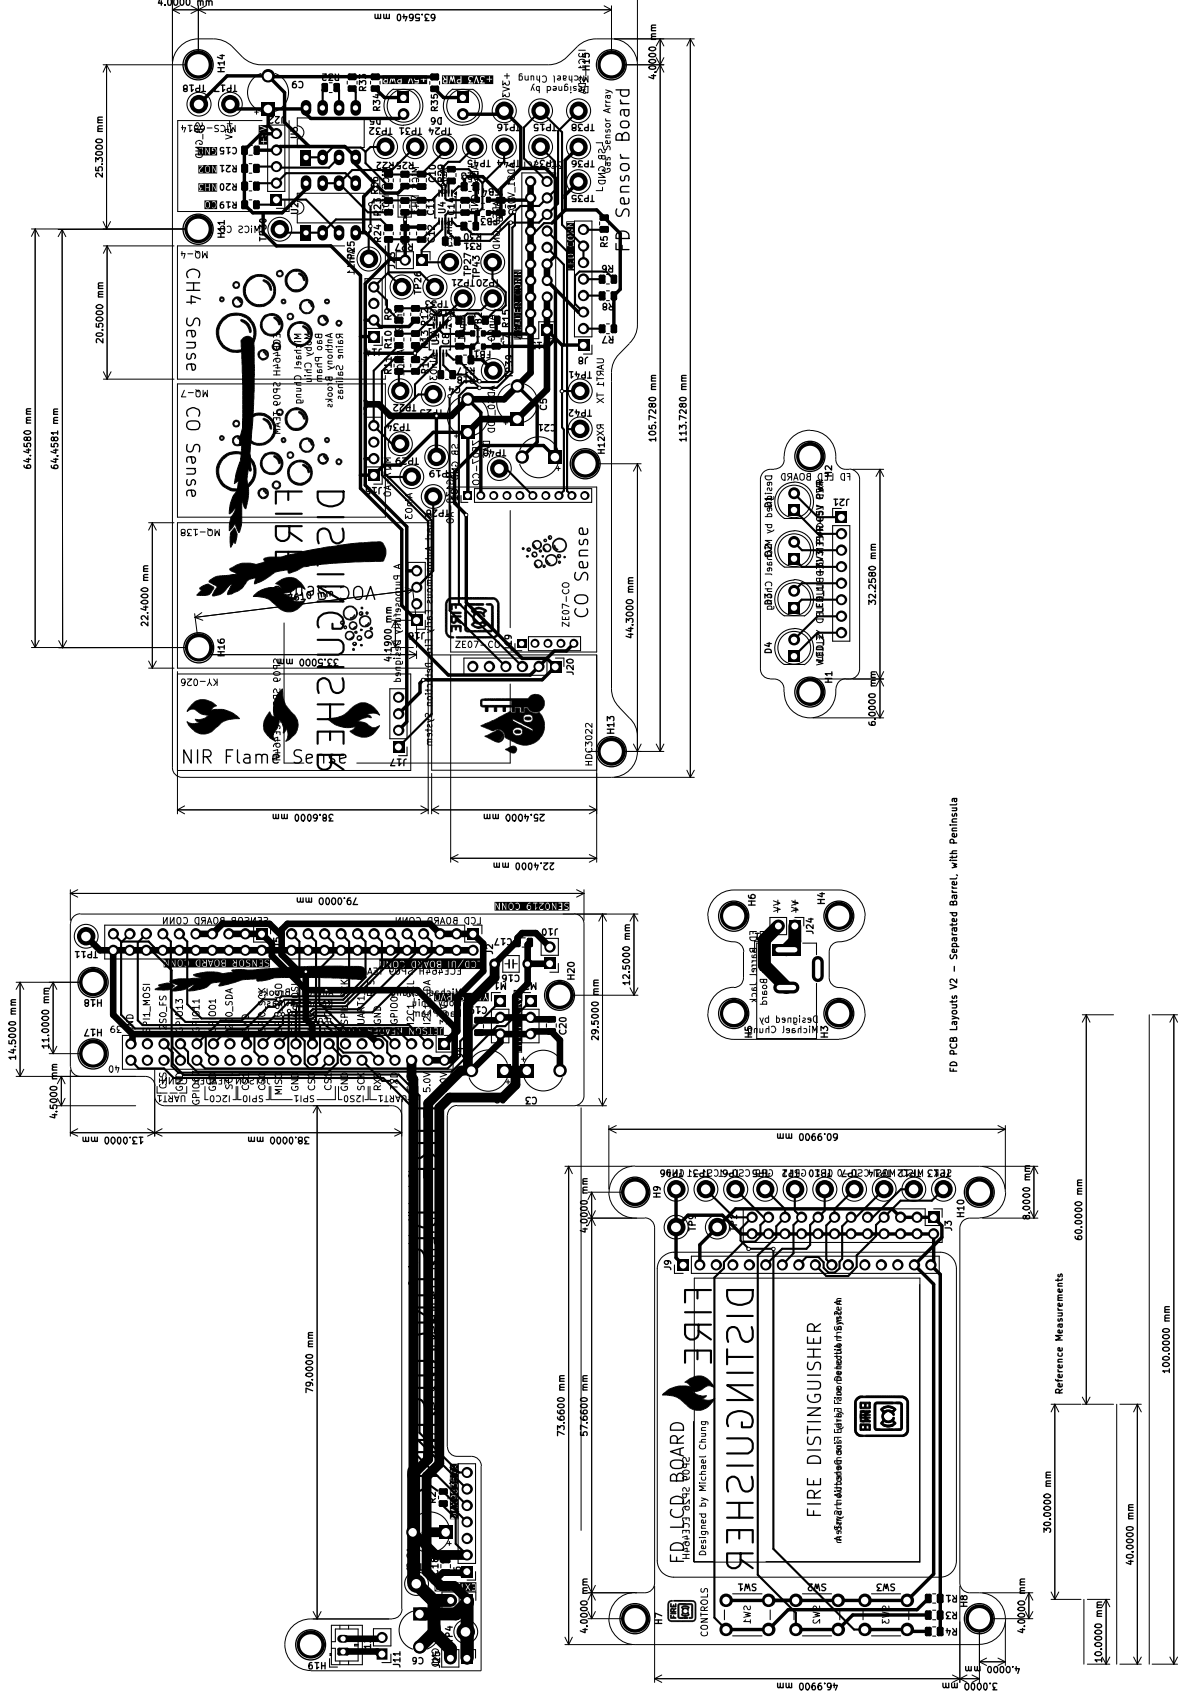
[picture p21: page 1]
