CaptainOrangeSparrow/early-fire-detection-classifier/hw/KiCAD/Paper_Prints/print8.pdf

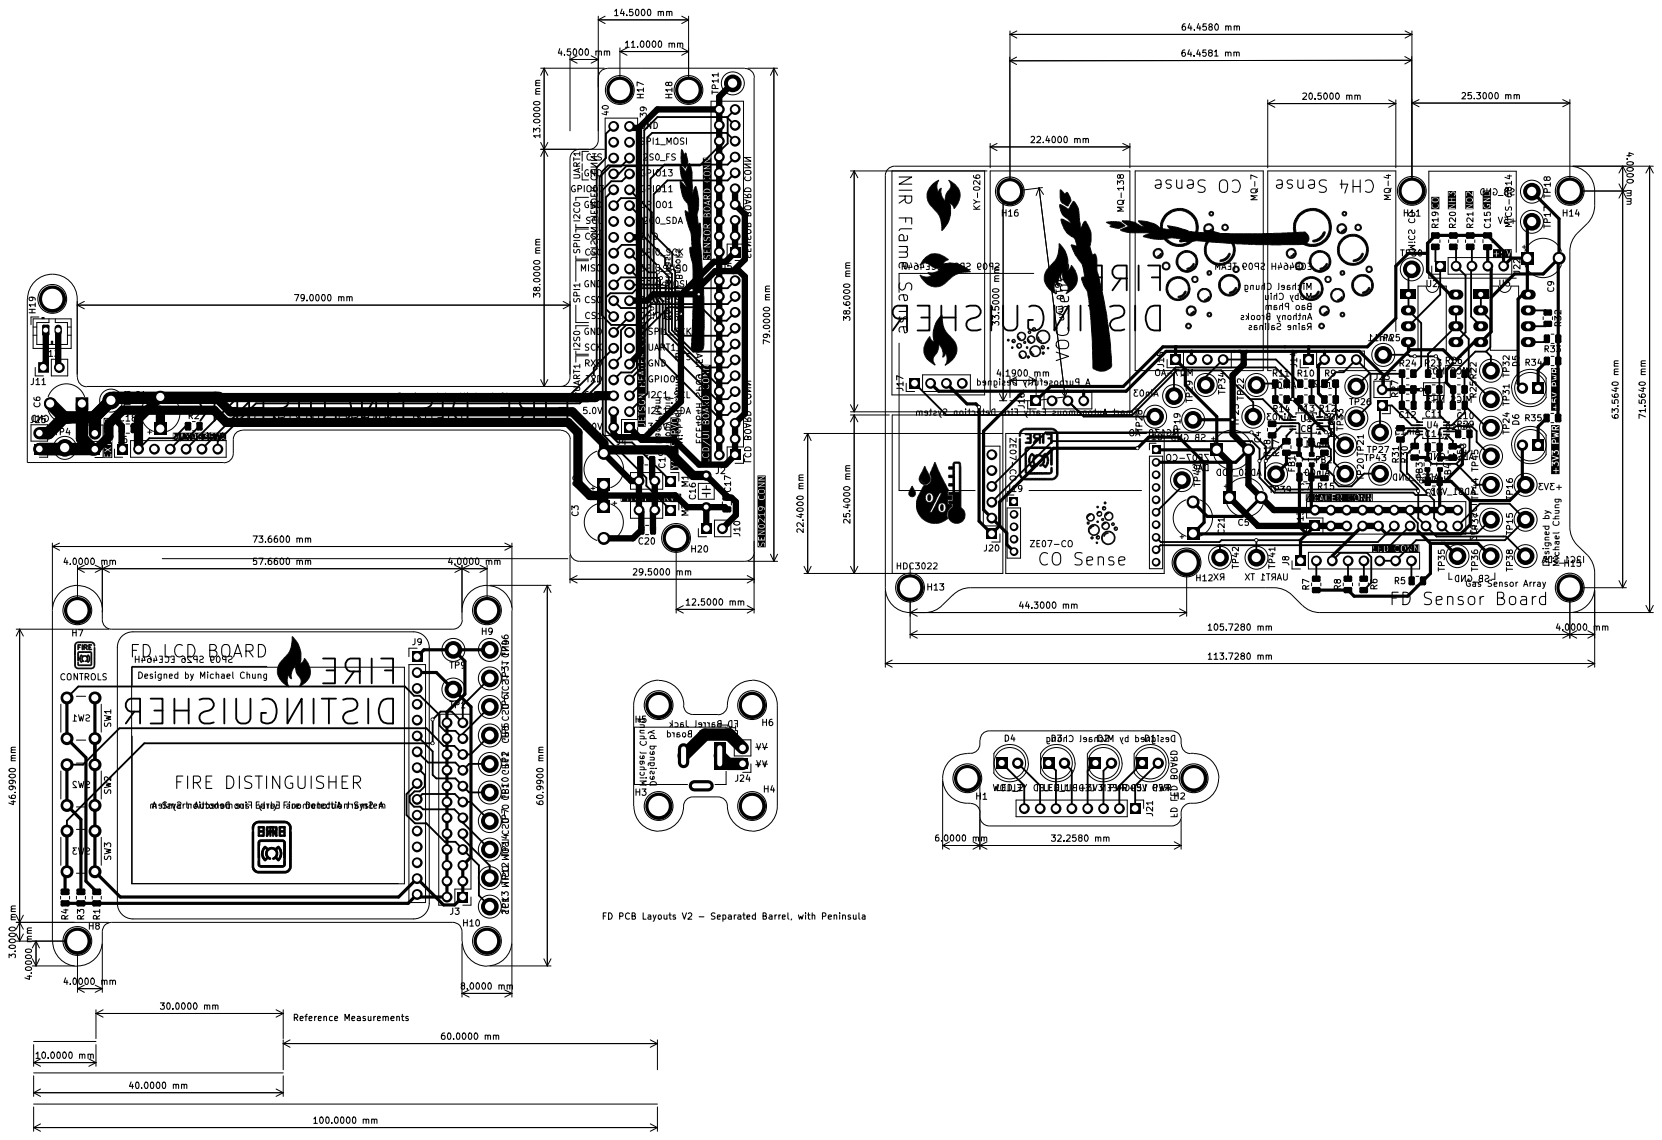
[picture p22: page 1]
