CaptainOrangeSparrow/early-fire-detection-classifier/hw/KiCAD/Paper_Prints/print9-104.pdf

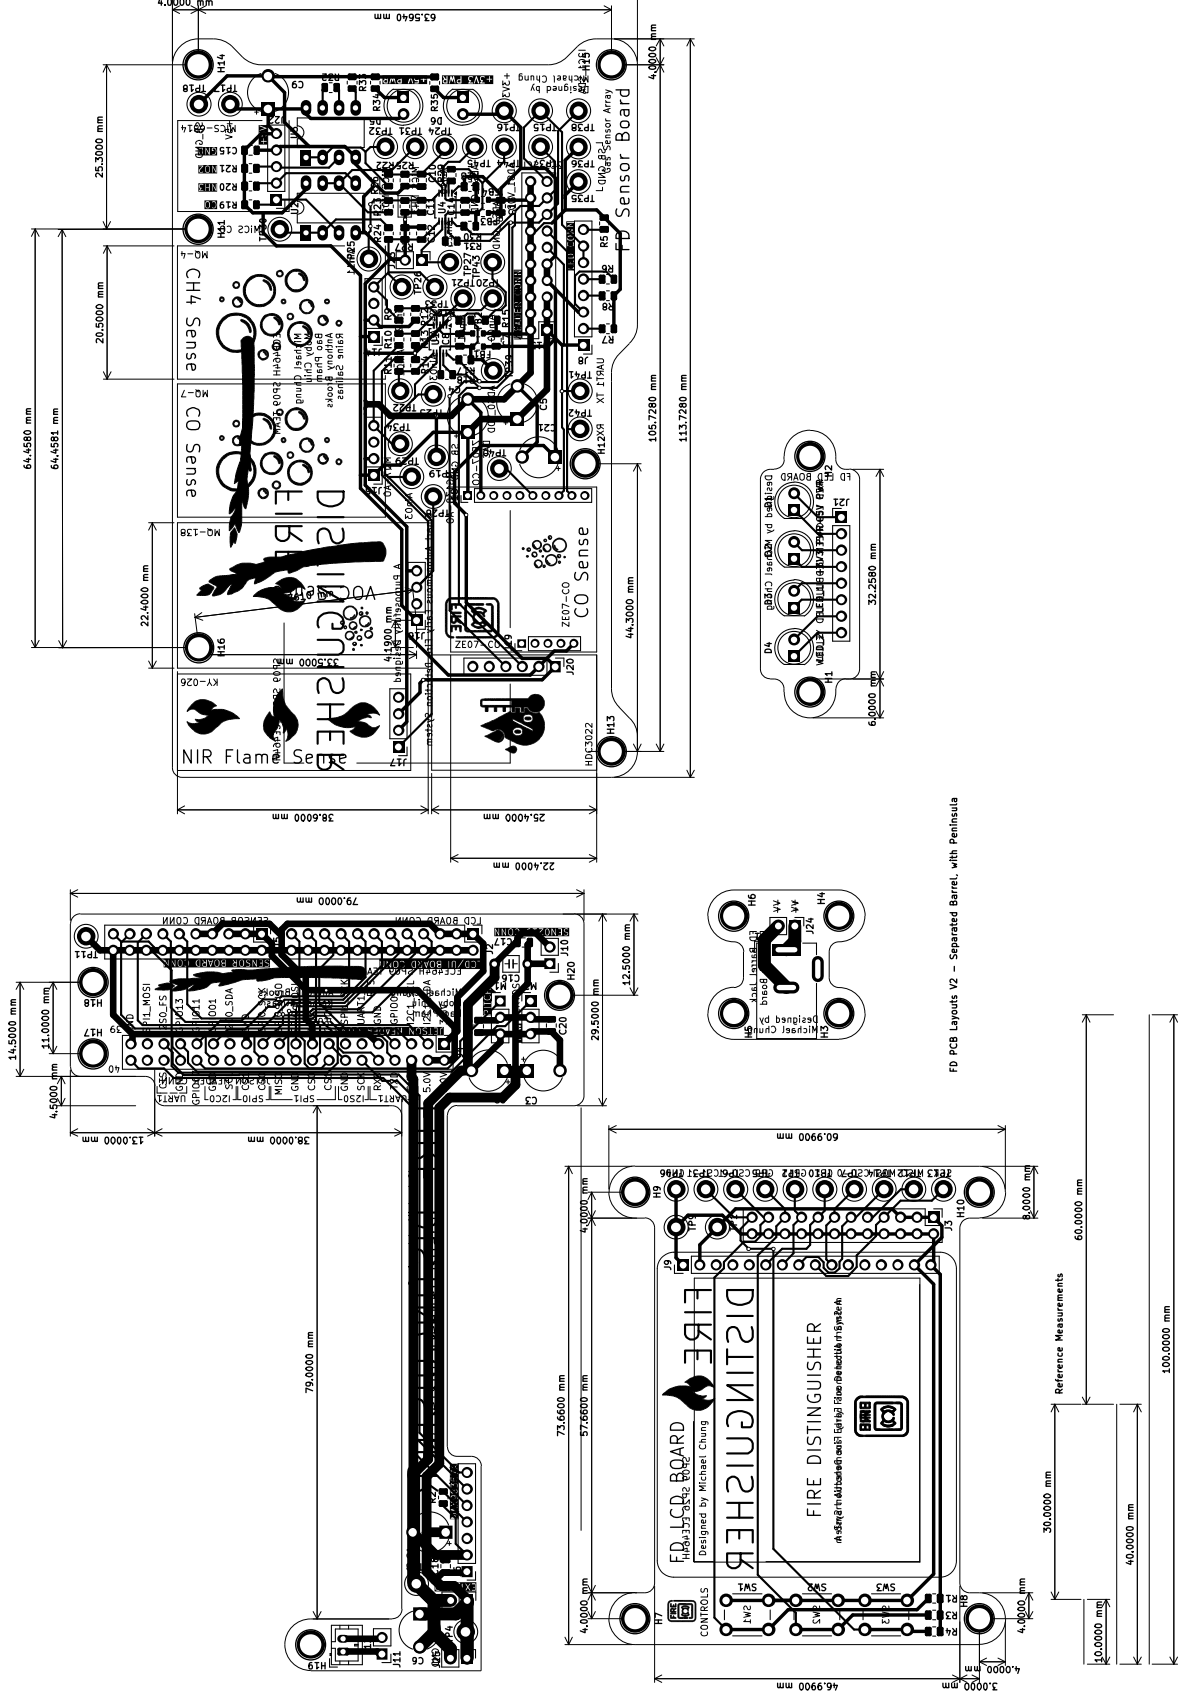
[picture p23: page 1]
