CaptainOrangeSparrow/early-fire-detection-classifier/hw/KiCAD/Paper_Prints/print9.pdf

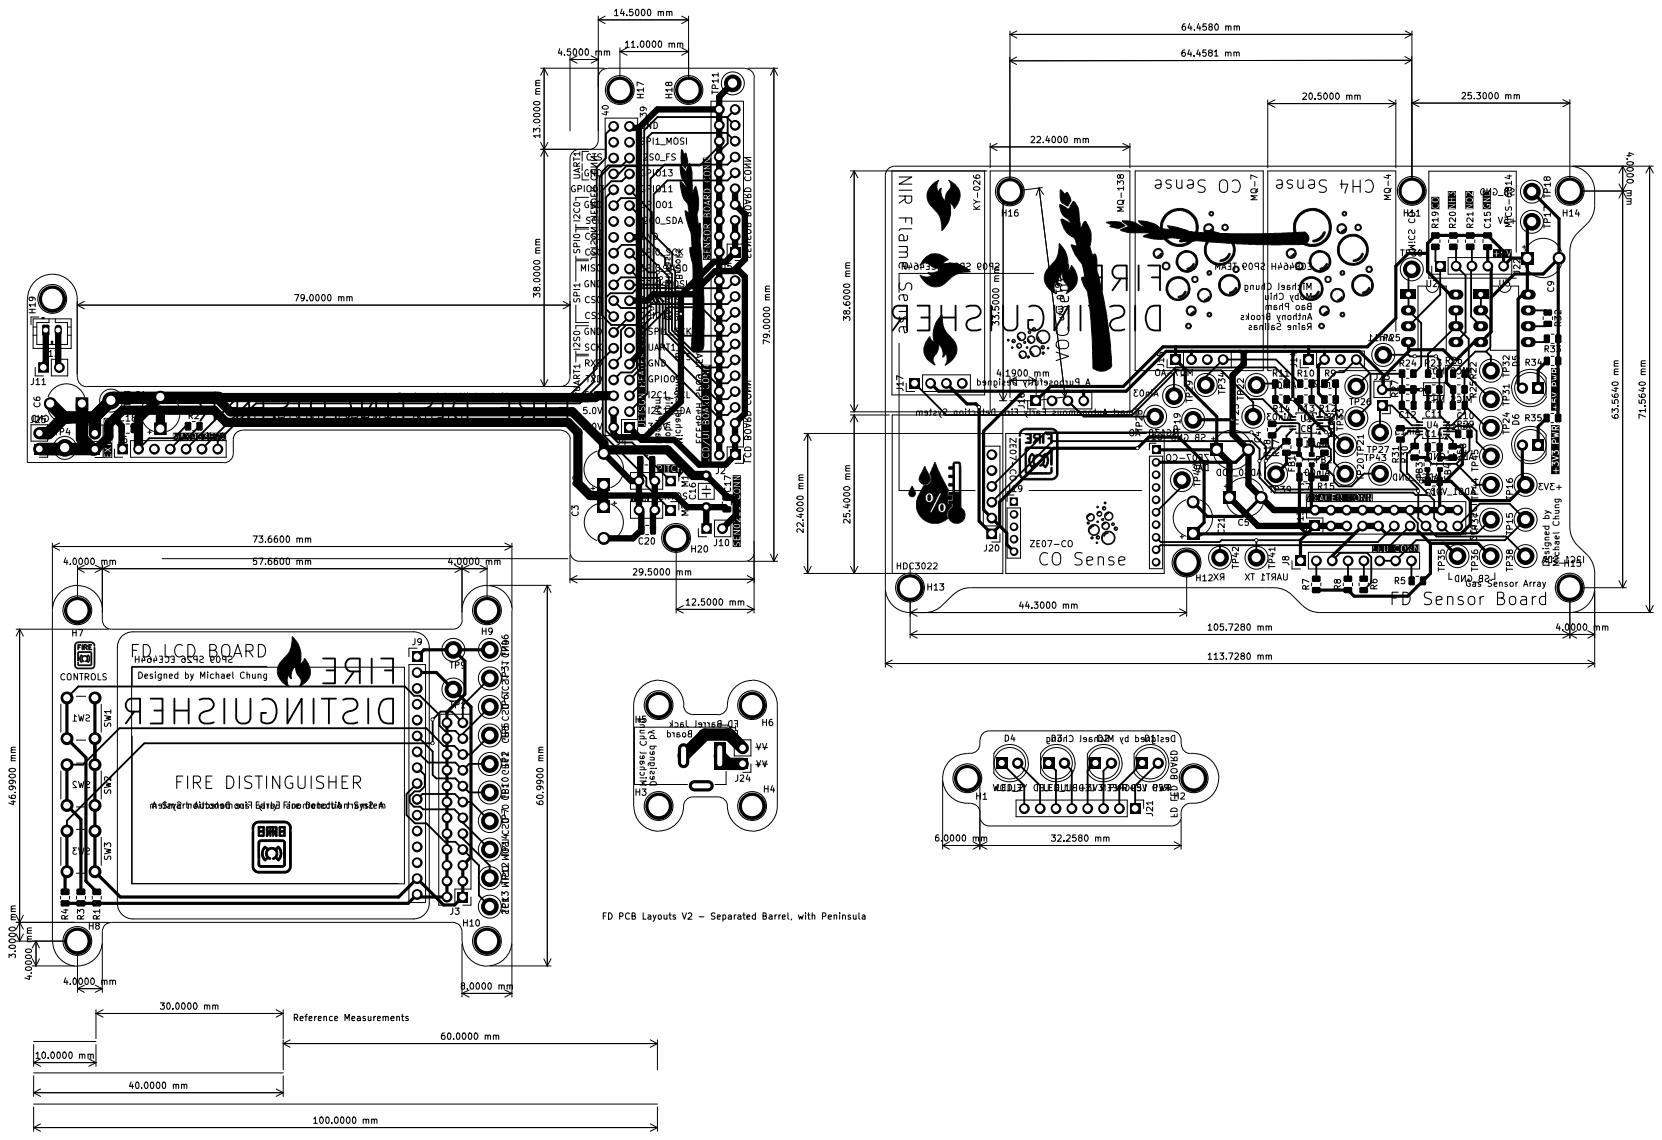
[picture p24: page 1]
