CaptainOrangeSparrow/early-fire-detection-classifier/live-fire-detection/constants.py

# Constants / Parameters used to configure the system

# Main program constants
FPS = 25 # Update frequency in Hz.
IR_CAMERA_DEVICE_ID = 2
REG_CAMERA_DEVICE_ID = 0

IR_COLORMAP = "INFERNO"
RECORDINGS_PARENT_DIR = "recordings_output"
